MotorDynamicsLab/LDOVoron0/Images/Kirigami/a_side_cable_run.jpg

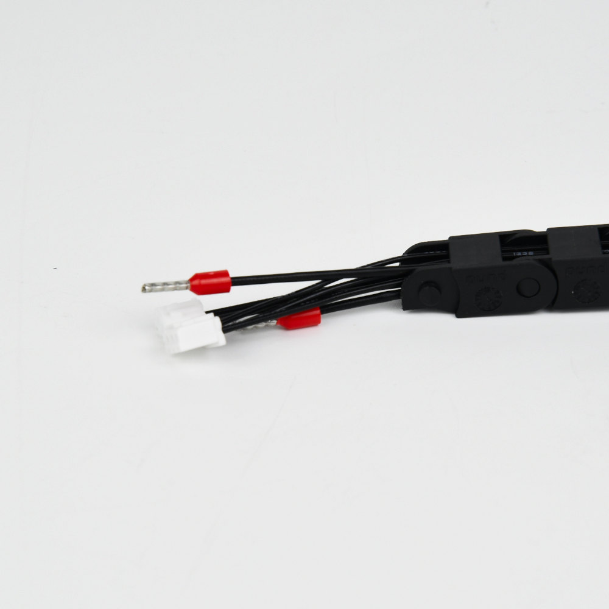
Images/Kirigami/a_side_cable_run.jpg
