MotorDynamicsLab/LDOVoron0/Images/Kirigami/cable_chain_skirt_anchor.JPG

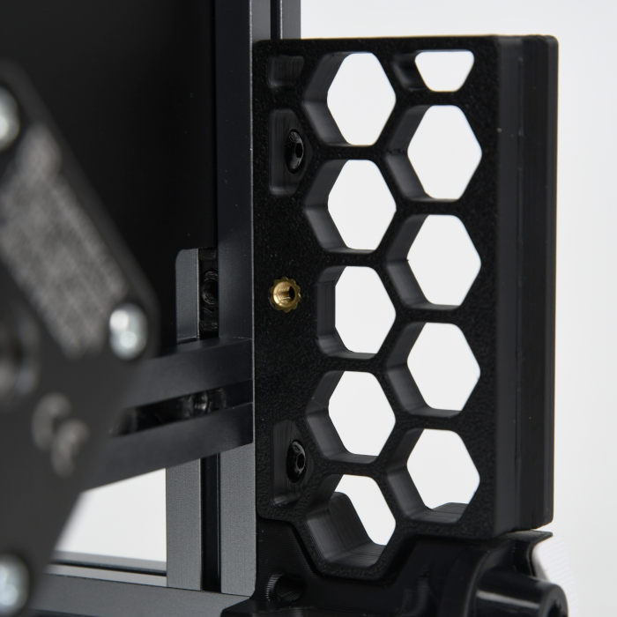
Images/Kirigami/cable_chain_skirt_anchor.JPG
