MotorDynamicsLab/LDOVoron0/Images/Kirigami/cable_ends_labelled.jpg

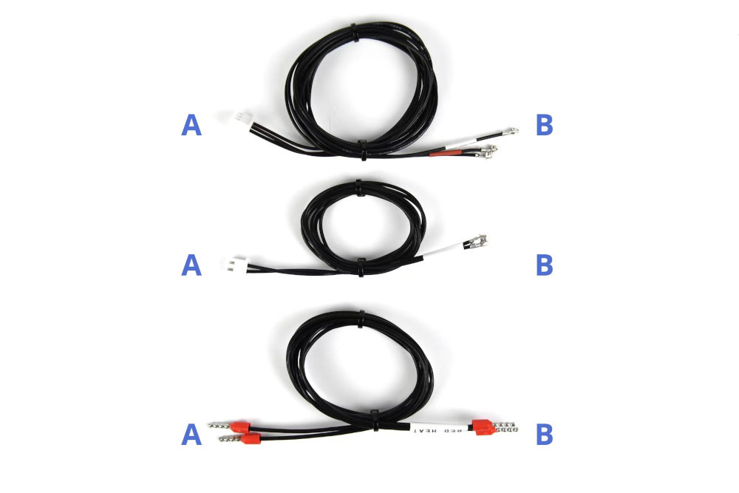
Images/Kirigami/cable_ends_labelled.jpg
