MotorDynamicsLab/LDOVoron0/Images/Kirigami/chain_end_locations.jpg

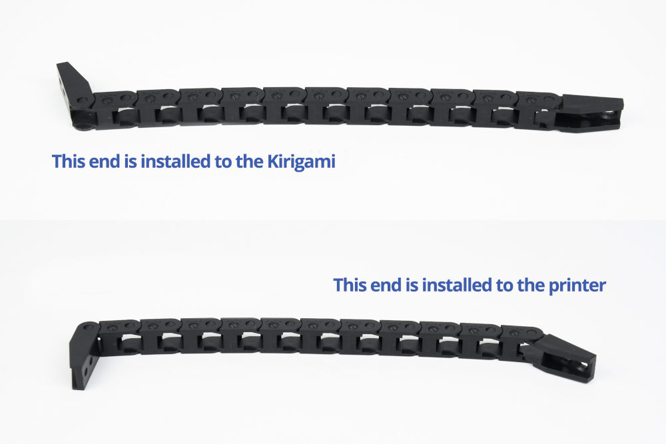
Images/Kirigami/chain_end_locations.jpg
