MotorDynamicsLab/LDOVoron0/Images/Kirigami/chain_ends_labelled.jpg

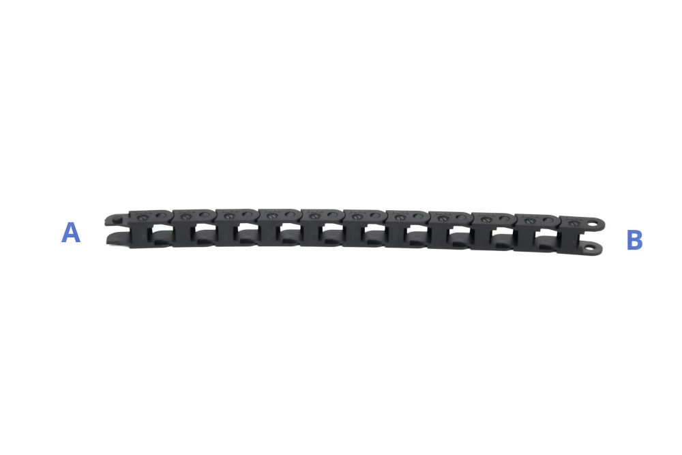
Images/Kirigami/chain_ends_labelled.jpg
