MotorDynamicsLab/LDOVoron0/Images/Kirigami/chain_height_check.JPG

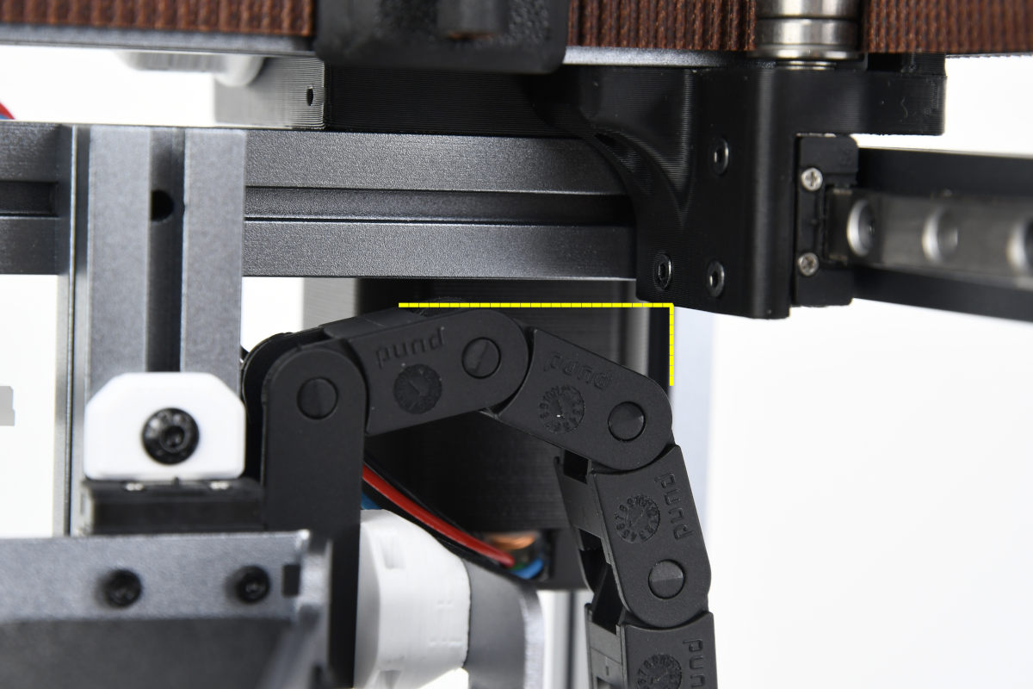
Images/Kirigami/chain_height_check.JPG
