MotorDynamicsLab/LDOVoron0/Images/Kirigami/neopixel_ziptied.JPG

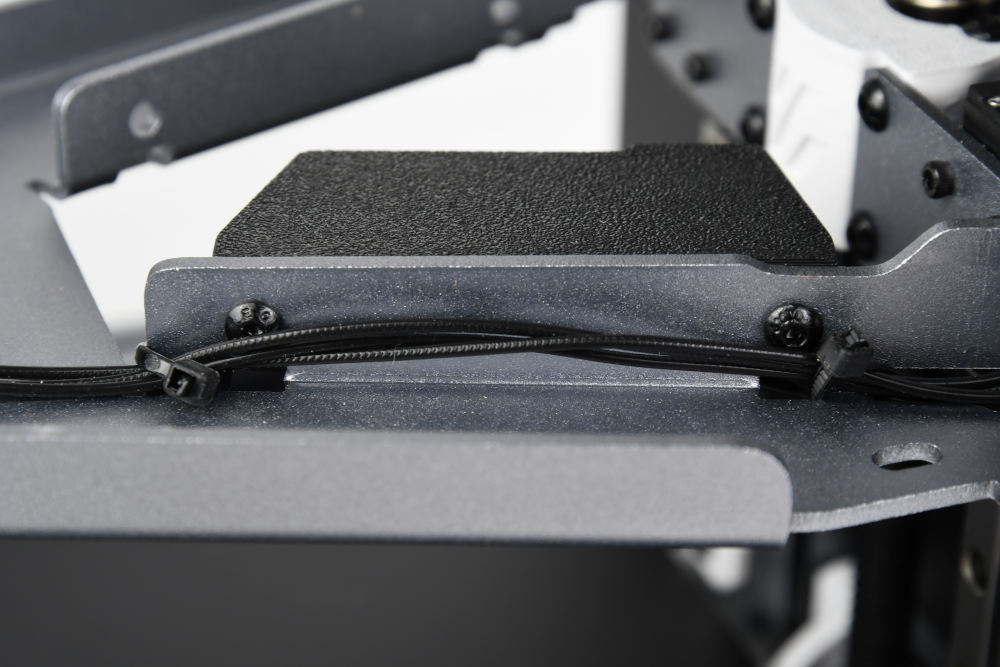
Images/Kirigami/neopixel_ziptied.JPG
