MotorDynamicsLab/LDOVoron0/Images/Kirigami/R1/bare_kirigami.jpg

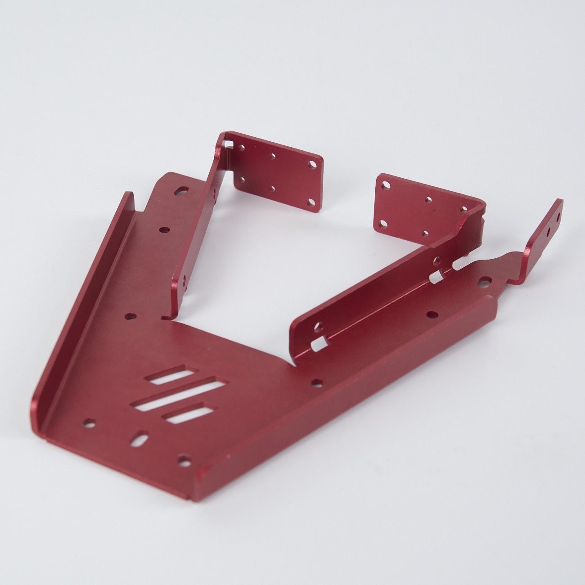
Images/Kirigami/R1/bare_kirigami.jpg
