MotorDynamicsLab/LDOVoron0/Images/Kirigami/R1/cable_layout_bottom.jpg

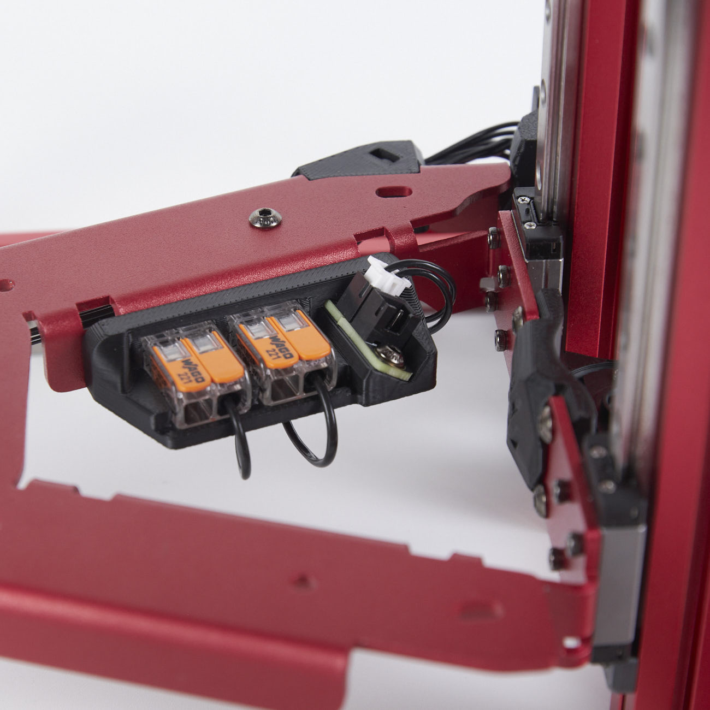
Images/Kirigami/R1/cable_layout_bottom.jpg
