MotorDynamicsLab/LDOVoron0/Images/Kirigami/R1/cable_layout_top.jpg

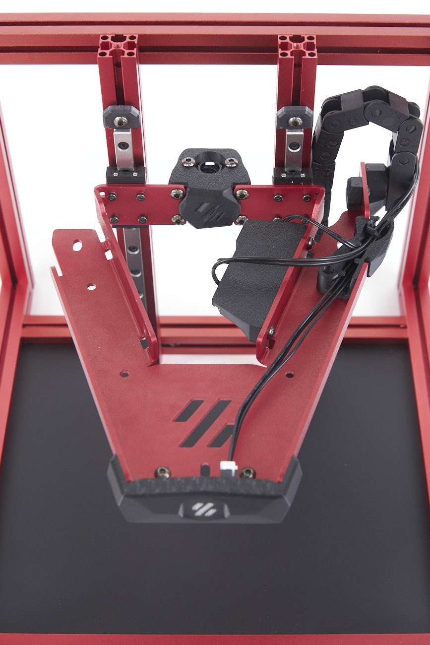
Images/Kirigami/R1/cable_layout_top.jpg
