MotorDynamicsLab/LDOVoron0/Images/Kirigami/R1/chain_mount.jpg

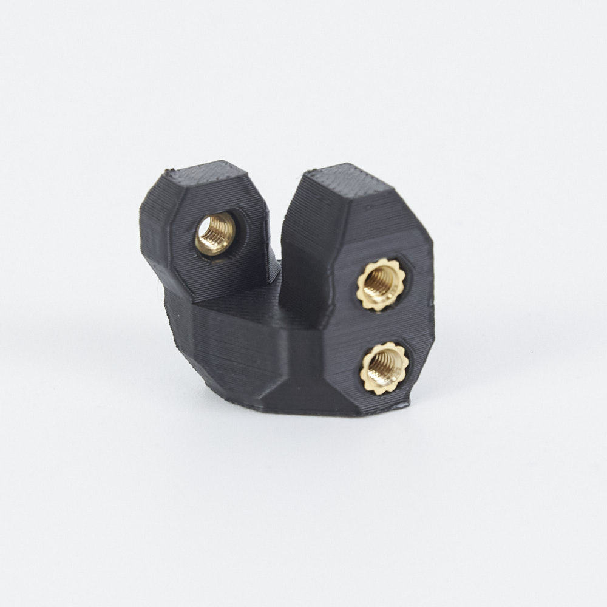
Images/Kirigami/R1/chain_mount.jpg
