MotorDynamicsLab/LDOVoron0/Images/Kirigami/R1/chain_with_cables.jpg

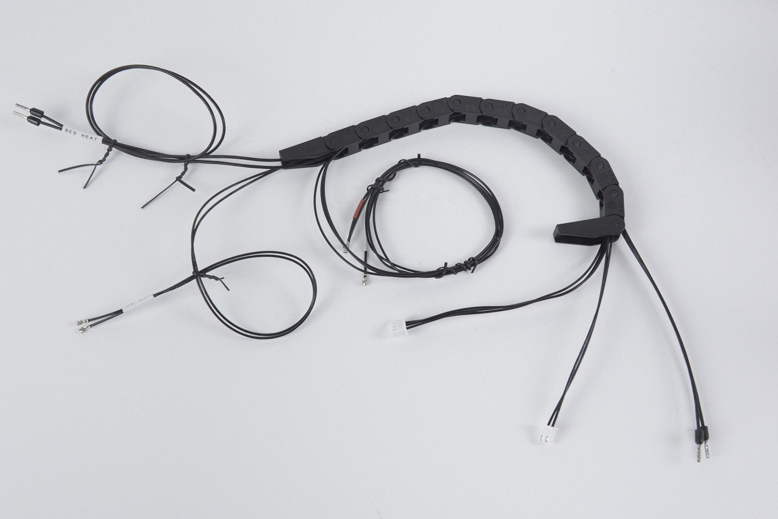
Images/Kirigami/R1/chain_with_cables.jpg
