MotorDynamicsLab/LDOVoron0/Images/Kirigami/R1/neopixel_pinout.jpg

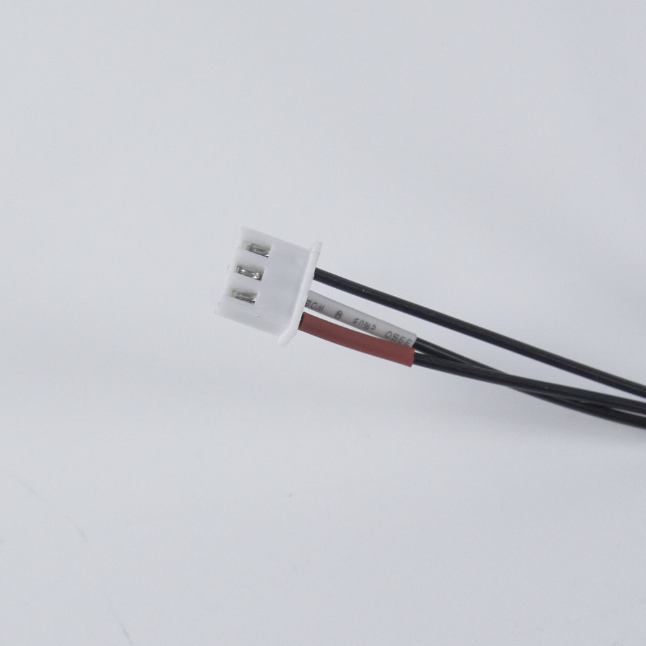
Images/Kirigami/R1/neopixel_pinout.jpg
