MotorDynamicsLab/LDOVoron0/Images/Kirigami/R1/nut_block_back.jpg

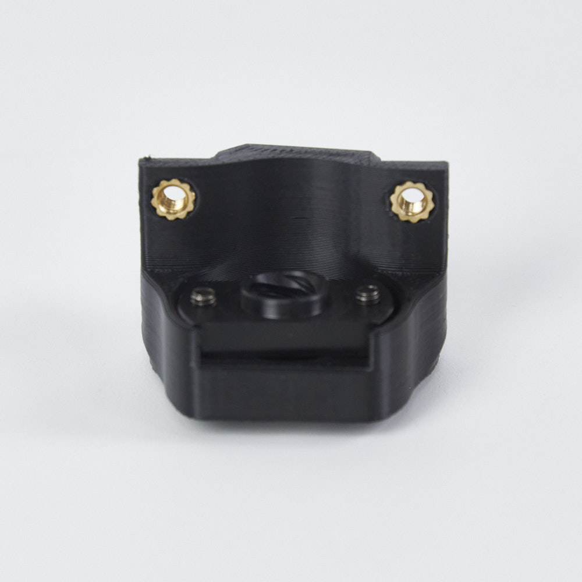
Images/Kirigami/R1/nut_block_back.jpg
