MotorDynamicsLab/LDOVoron0/Images/Kirigami/R1/nut_block_front.jpg

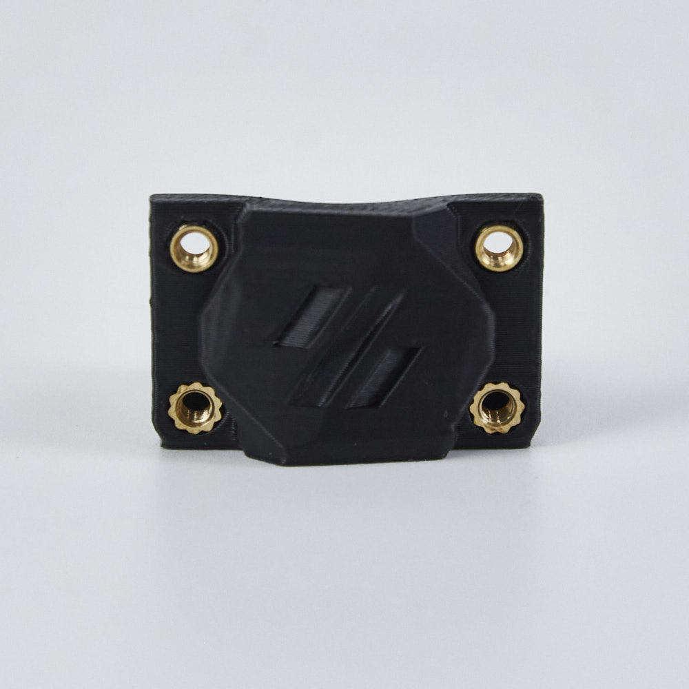
Images/Kirigami/R1/nut_block_front.jpg
