MotorDynamicsLab/LDOVoron0/Images/Kirigami/R1/sb_front_with_cable.jpg

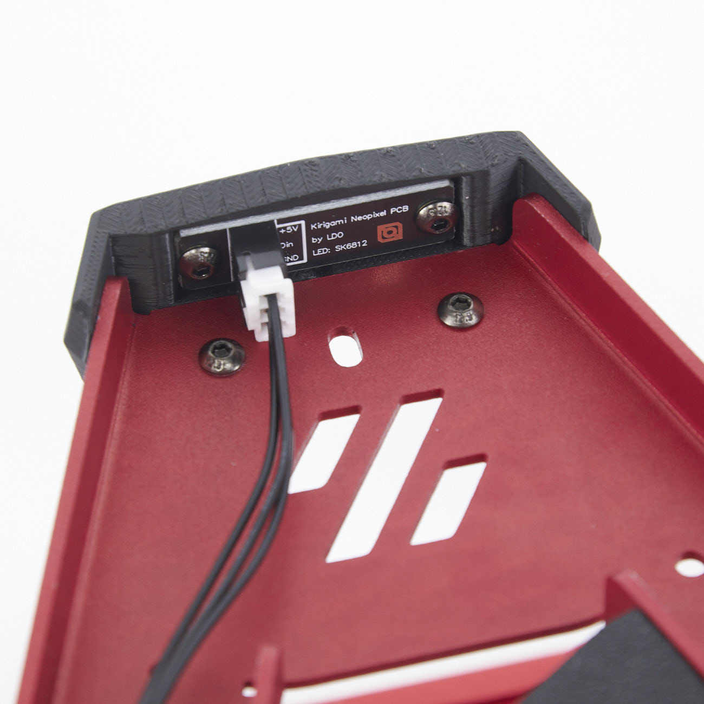
Images/Kirigami/R1/sb_front_with_cable.jpg
