MotorDynamicsLab/LDOVoron0/Images/Kirigami/R1/stealth_front_bottom.jpg

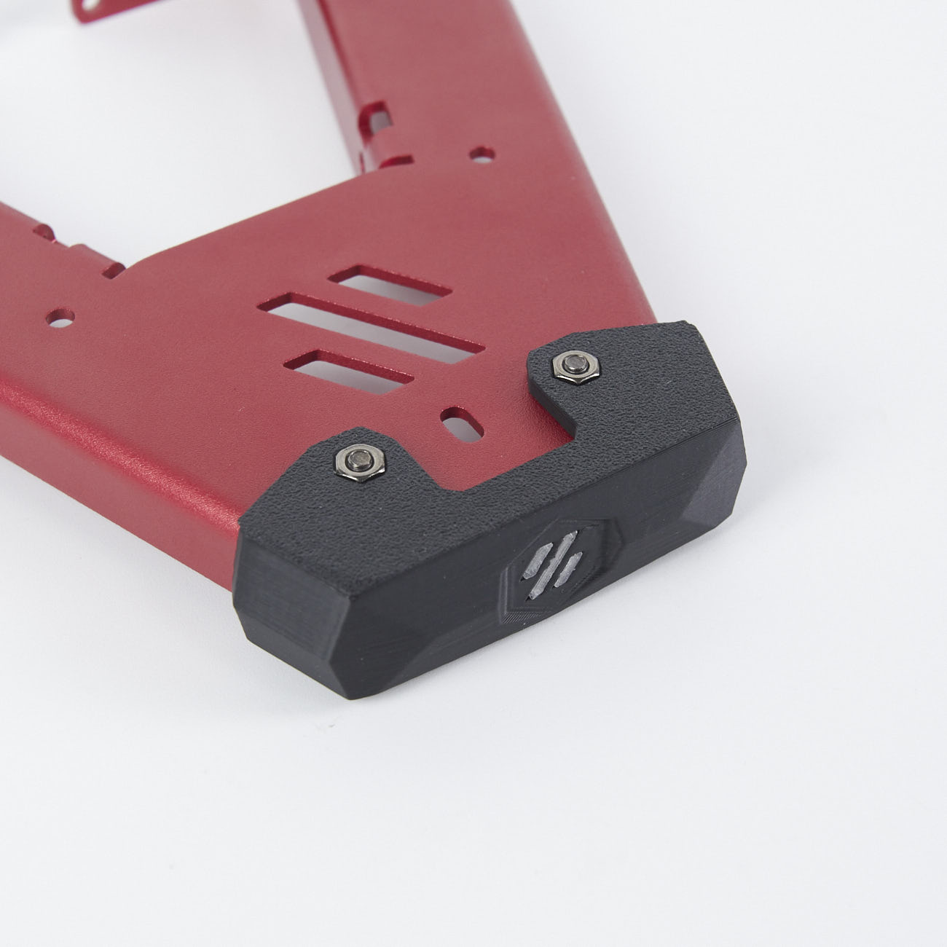
Images/Kirigami/R1/stealth_front_bottom.jpg
