MotorDynamicsLab/LDOVoron0/Images/Kirigami/R1/stealth_front_with_diffuser.jpg

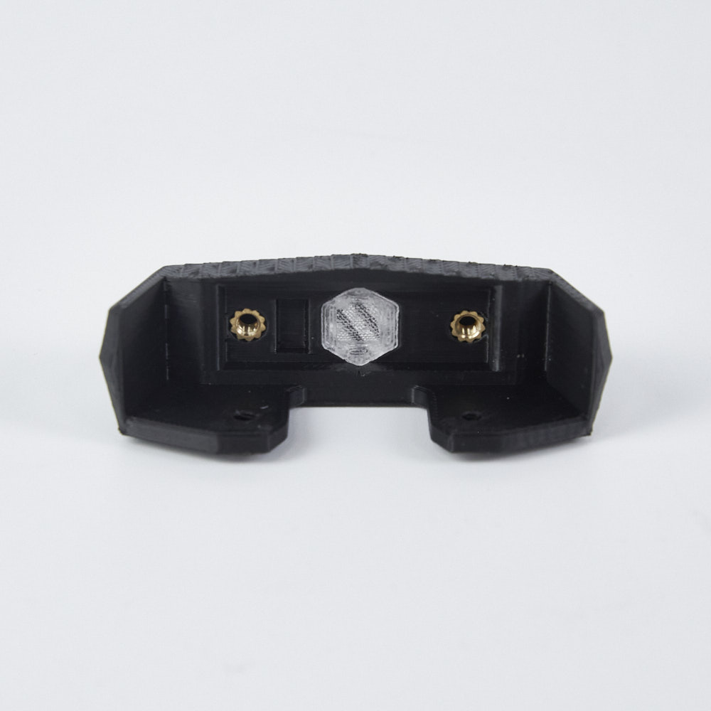
Images/Kirigami/R1/stealth_front_with_diffuser.jpg
