MotorDynamicsLab/LDOVoron0/Images/Kirigami/R1/stealth_front_with_pcb.jpg

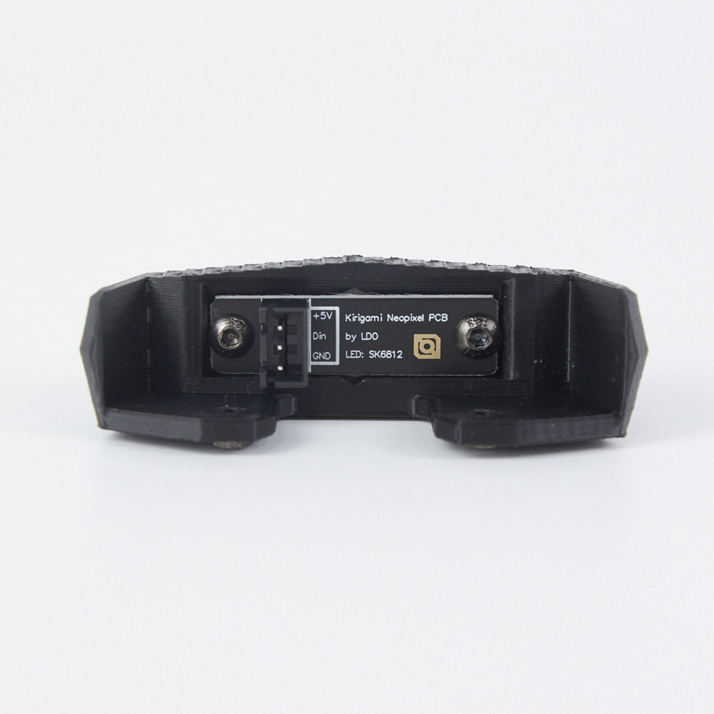
Images/Kirigami/R1/stealth_front_with_pcb.jpg
