MotorDynamicsLab/LDOVoron0/Images/Kirigami/R1/tramming_view.jpg

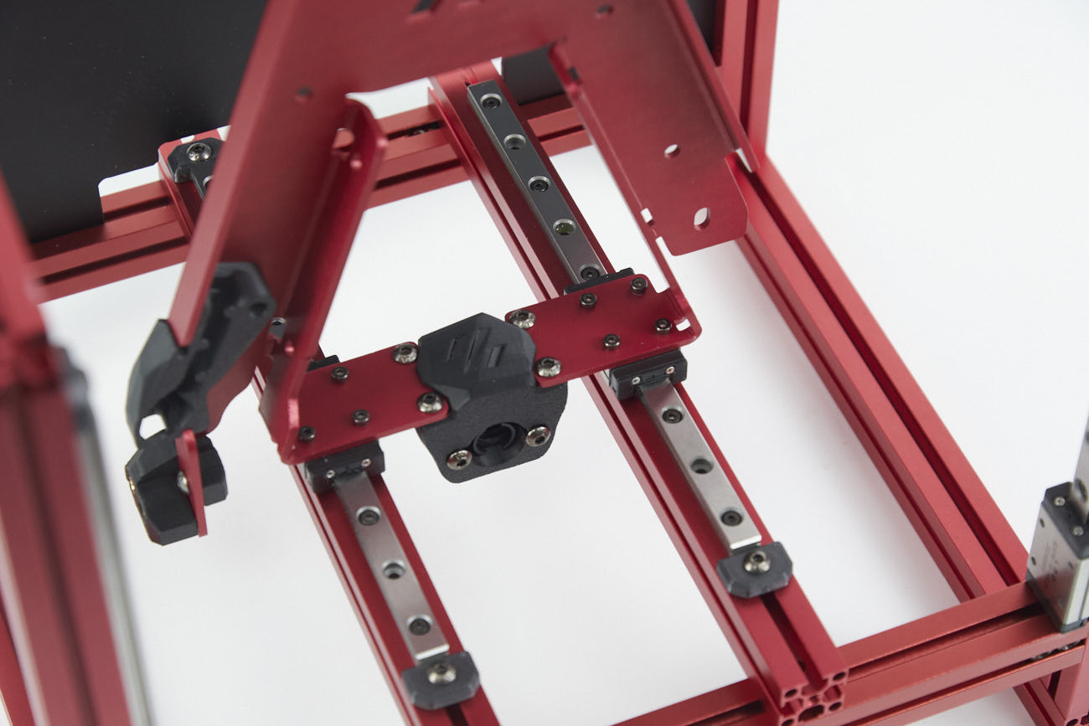
Images/Kirigami/R1/tramming_view.jpg
