MotorDynamicsLab/LDOVoron0/Images/Kirigami/R1/wago_mount_back.jpg

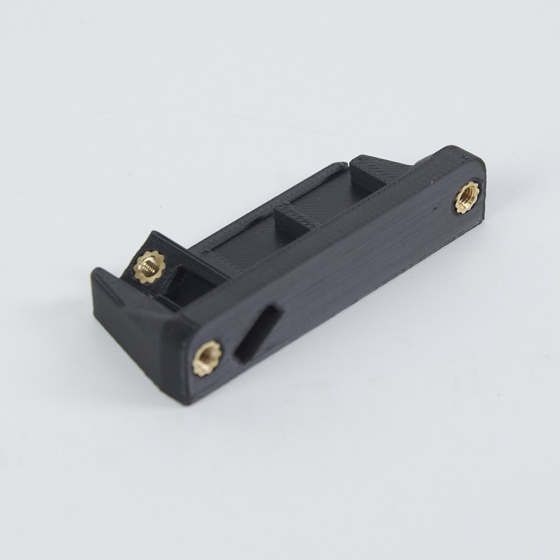
Images/Kirigami/R1/wago_mount_back.jpg
