MotorDynamicsLab/LDOVoron0/Images/Kirigami/R1/wago_mount_front.jpg

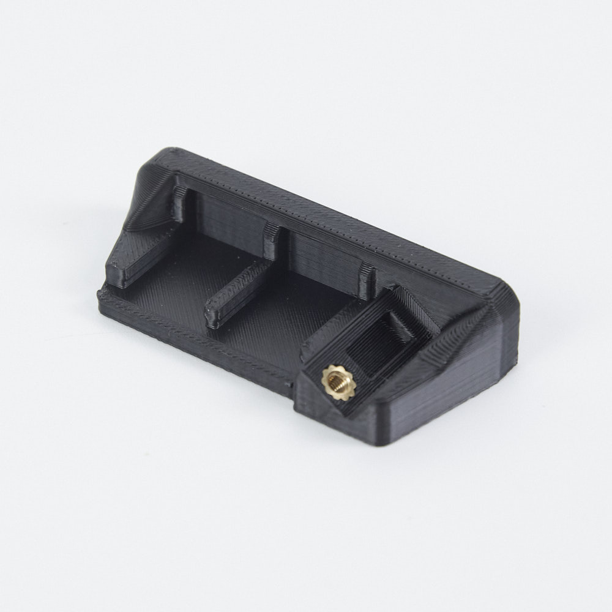
Images/Kirigami/R1/wago_mount_front.jpg
