MotorDynamicsLab/LDOVoron0/Images/split_rear_panel_cad.png

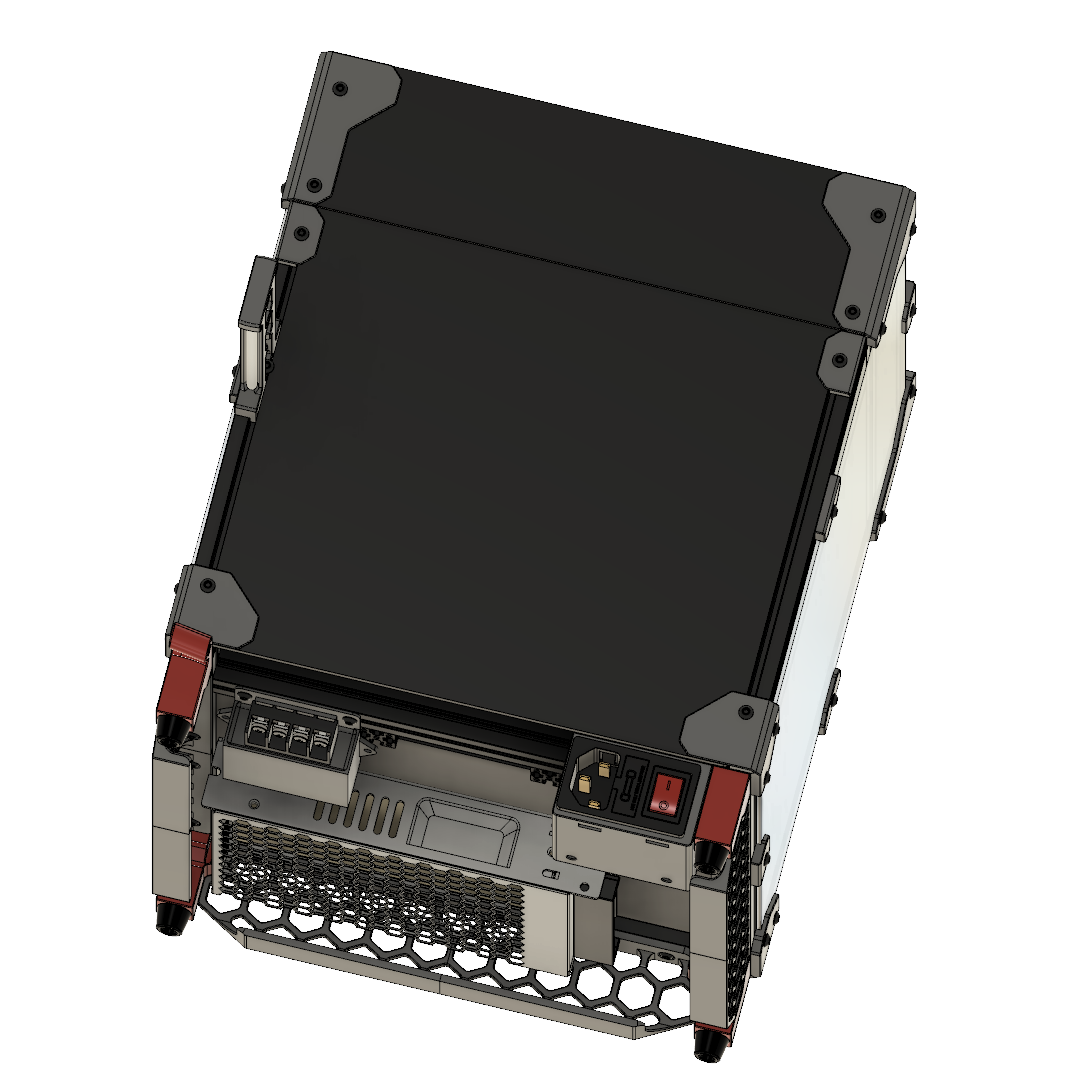
Images/split_rear_panel_cad.png
