MotorDynamicsLab/LDOVoron0/Images/Kirigami/R1/printed_parts_installed.jpg

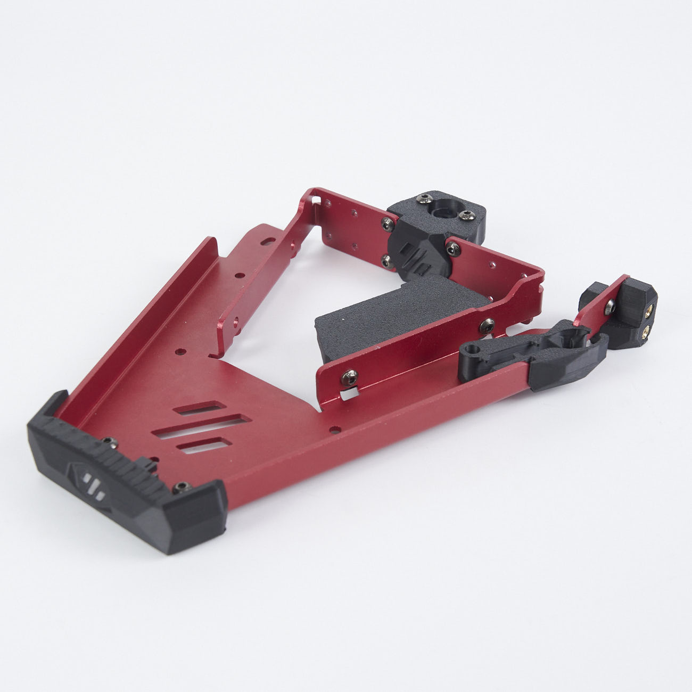
Images/Kirigami/R1/printed_parts_installed.jpg
