MotorDynamicsLab/LDOVoron0/STLs/Detachable_Spool_Holder/Spool_Holder.stl

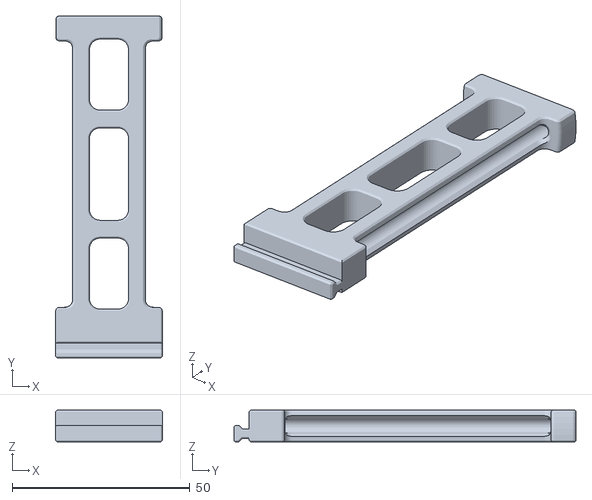
[picture p40: CAD file, 2023-02-16]
STLs/Detachable_Spool_Holder/Spool_Holder.stl
30.0 x 96.2 x 9.00
