MotorDynamicsLab/LDOVoron0/STLs/DIN_Mounts/SKR Pico Mount_x2.step

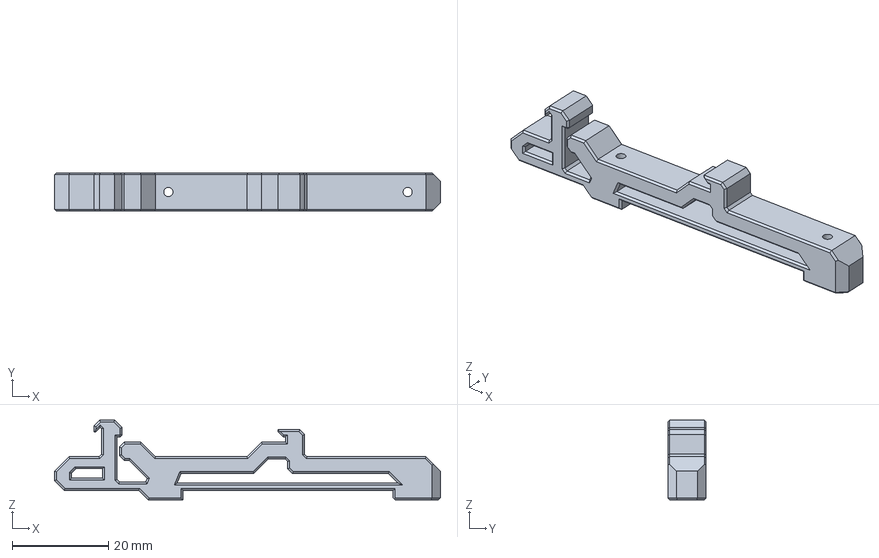
[picture p41: CAD file, 2023-02-05]
STLs/DIN_Mounts/SKR Pico Mount_x2.step
80.3 x 8.00 x 16.6 mm
