MotorDynamicsLab/LDOVoron0/STLs/Kirigami/Kirigami_LDO_Breakout_Mount.stl

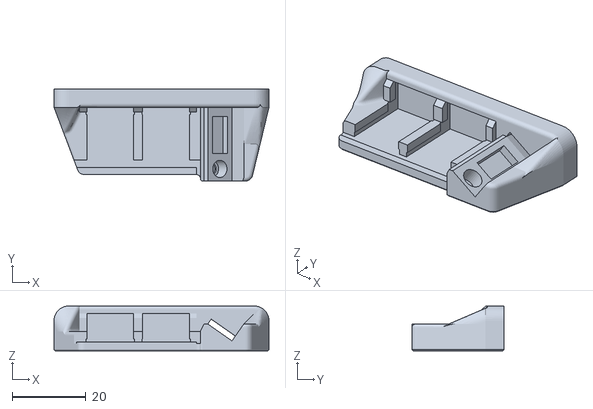
[picture p42: CAD file, 2023-02-16]
STLs/Kirigami/Kirigami_LDO_Breakout_Mount.stl
58.3 x 25.0 x 12.2
