MotorDynamicsLab/LDOVoron0/STLs/Name_Plate/Name_Plate_Top.stl

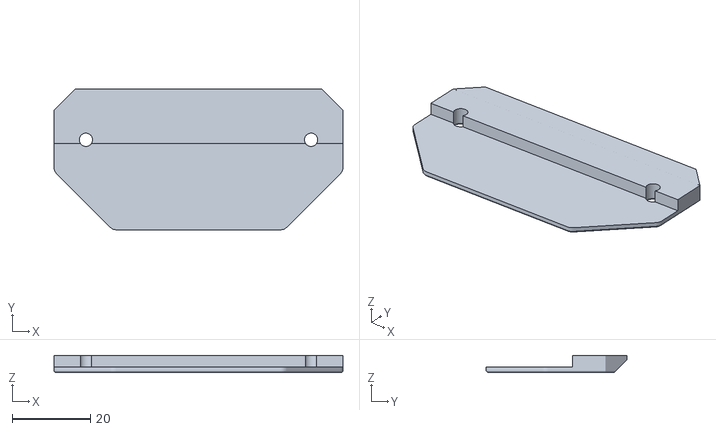
[picture p43: CAD file, 2023-02-16]
STLs/Name_Plate/Name_Plate_Top.stl
73.8 x 35.9 x 4.42
