MotorDynamicsLab/LDOVoron0/STLs/Picobilical_Toolhead/Picobilical_Strain_Relief_Spacer_A.stl

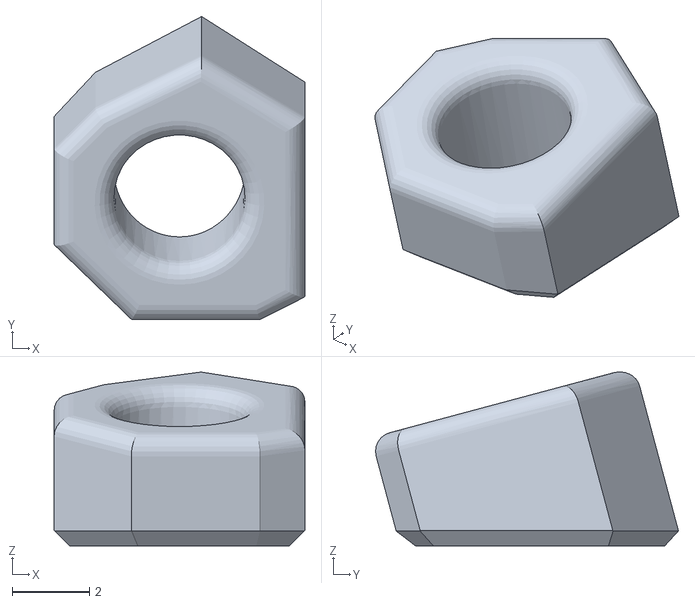
[picture p44: CAD file, 2023-02-16]
STLs/Picobilical_Toolhead/Picobilical_Strain_Relief_Spacer_A.stl
6.50 x 7.85 x 4.51
