MotorDynamicsLab/LDOVoron0/STLs/Preset_Print_PlatesR1/LDO_Electronics_Tools_Inlet_PlateR1.3mf

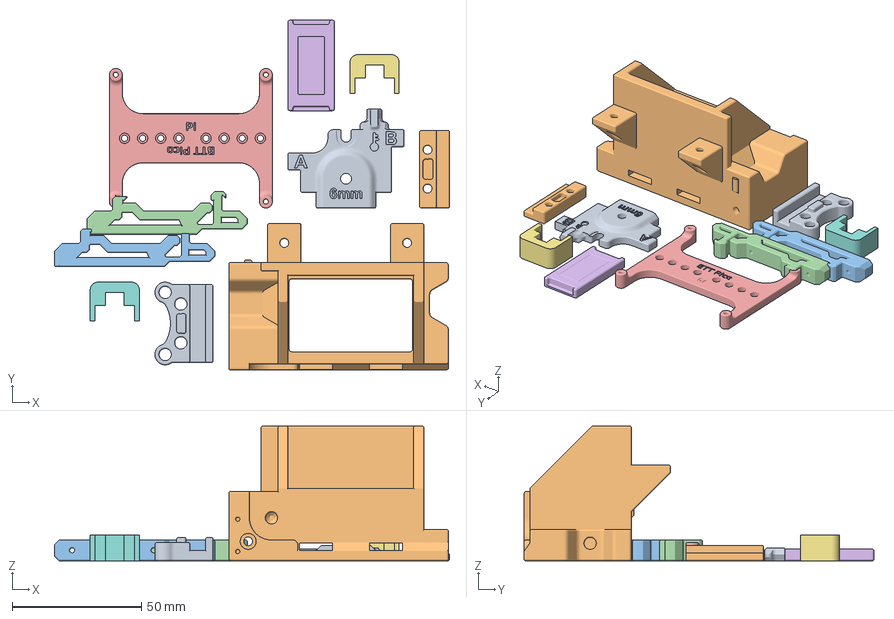
[picture p45: CAD file, 2023-06-14]
STLs/Preset_Print_PlatesR1/LDO_Electronics_Tools_Inlet_PlateR1.3mf
152.6 x 135.1 x 52.0 mm
Fan_Mount_Bottom_x1.stl
Fan_Mount_Top_x1.stl
PCB_DIN_Clip_x2.stl
RPi_or_BTT-Pico_Mount.STL
VHB_DIN_Mount.STL
MGN7_Rail_Guide_x2.STL
Swiss_Army_Jig_x1.STL
V02R1_Mains_Inlet Foot_1_2mm.stl
