MotorDynamicsLab/LDOVoron0/STLs/Picobilical_Toolhead/Picobilical_Strain_Relief_Extender_x2.stl

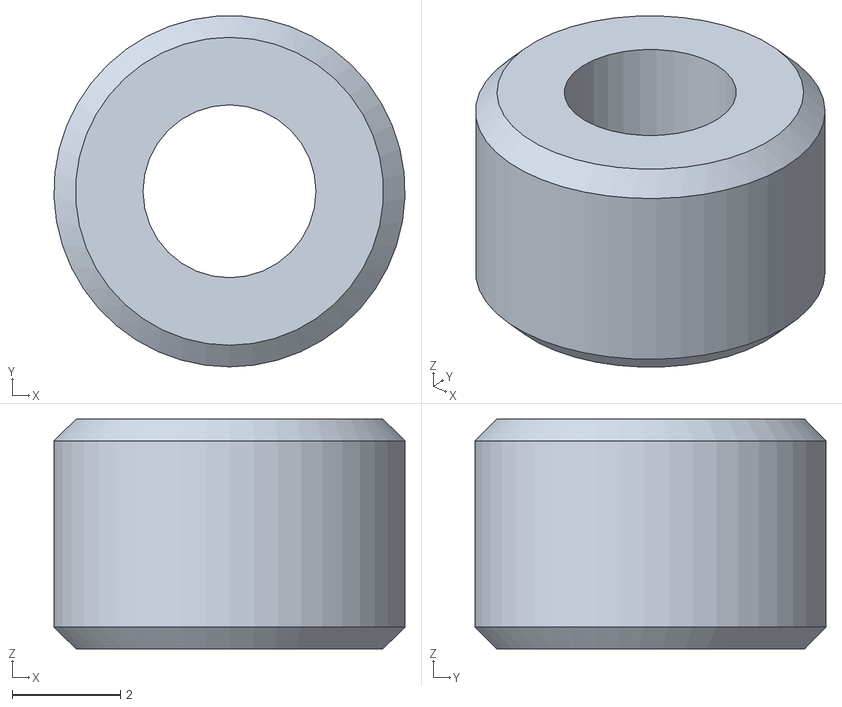
[picture p47: CAD file, 2023-02-16]
STLs/Picobilical_Toolhead/Picobilical_Strain_Relief_Extender_x2.stl
6.50 x 6.49 x 4.25
