MotorDynamicsLab/LDOVoron0/STLs/Preset_Print_PlatesR1/LDO_Skirts_PlateR1.3mf

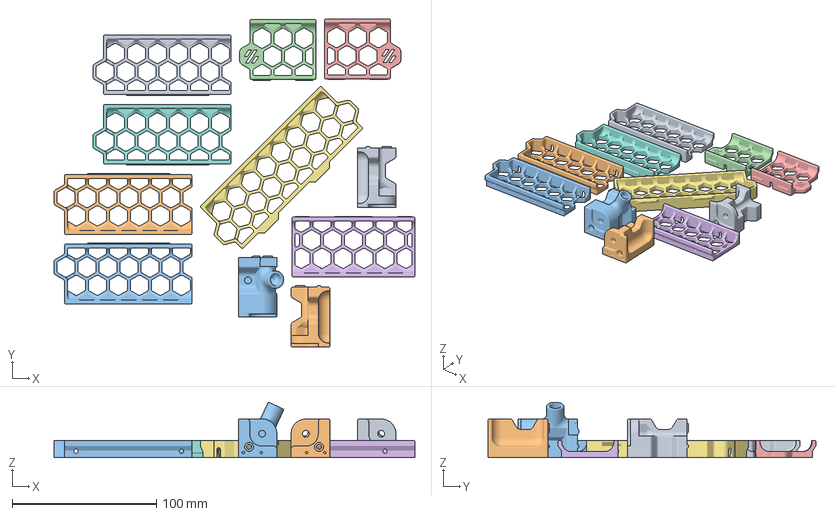
[picture p48: CAD file, 2023-06-14]
STLs/Preset_Print_PlatesR1/LDO_Skirts_PlateR1.3mf
250.0 x 227.2 x 38.4 mm
Foot_Front_Left_x1.STL
Foot_Front_Right_x1.STL
Foot_Rear_Right_FRS_x1.STL
Front_Skirt_A_x1.STL
Front_Skirt_B_x1.STL
Headless_Skirt_Insert.STL
Rear_Skirt_x1.STL
Side_Skirt_Mirror_x2.stl
Side_Skirt_x2.STL
