MotorDynamicsLab/LDOVoron0/STLs/Name_Plate/Name_Plate.stl

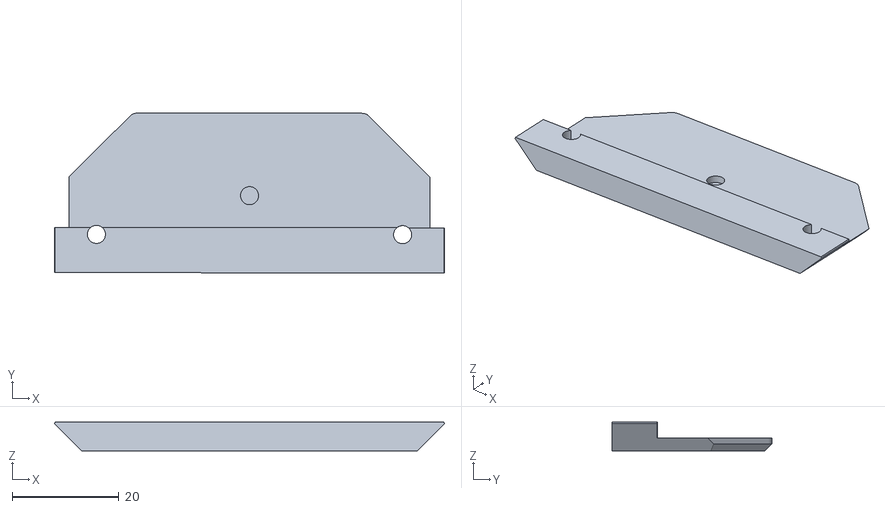
[picture p49: CAD file, 2023-02-16]
STLs/Name_Plate/Name_Plate.stl
73.2 x 30.0 x 5.40
