MotorDynamicsLab/LDOVoron0/STLs/Picobilical_Toolhead/Picobilical_Strain_Relief_Spacer_B.stl

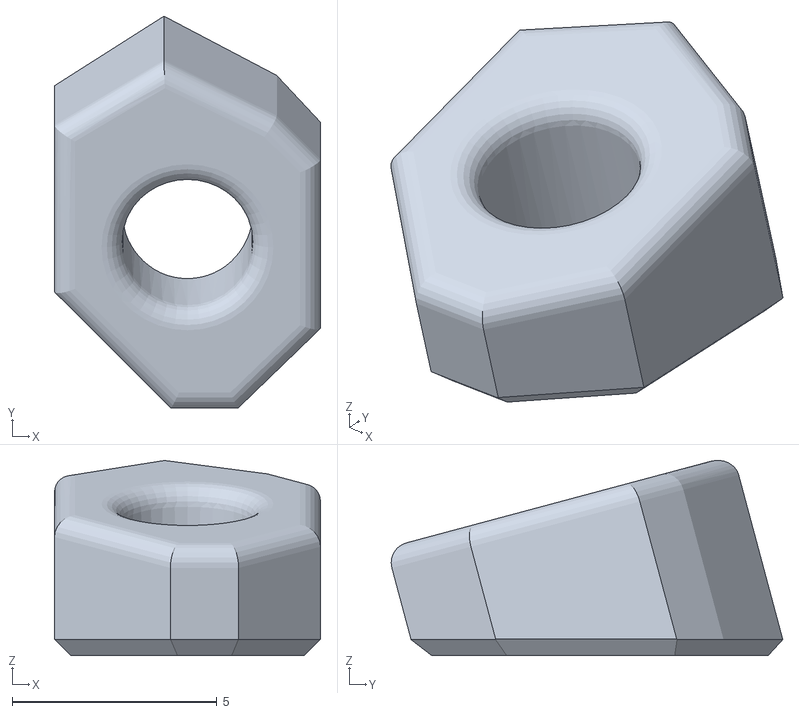
[picture p50: CAD file, 2023-02-16]
STLs/Picobilical_Toolhead/Picobilical_Strain_Relief_Spacer_B.stl
6.50 x 9.57 x 4.77
