MotorDynamicsLab/LDOVoron0/STLs/Picobilical_Toolhead/Picobilical Toolhead Mount V02.step

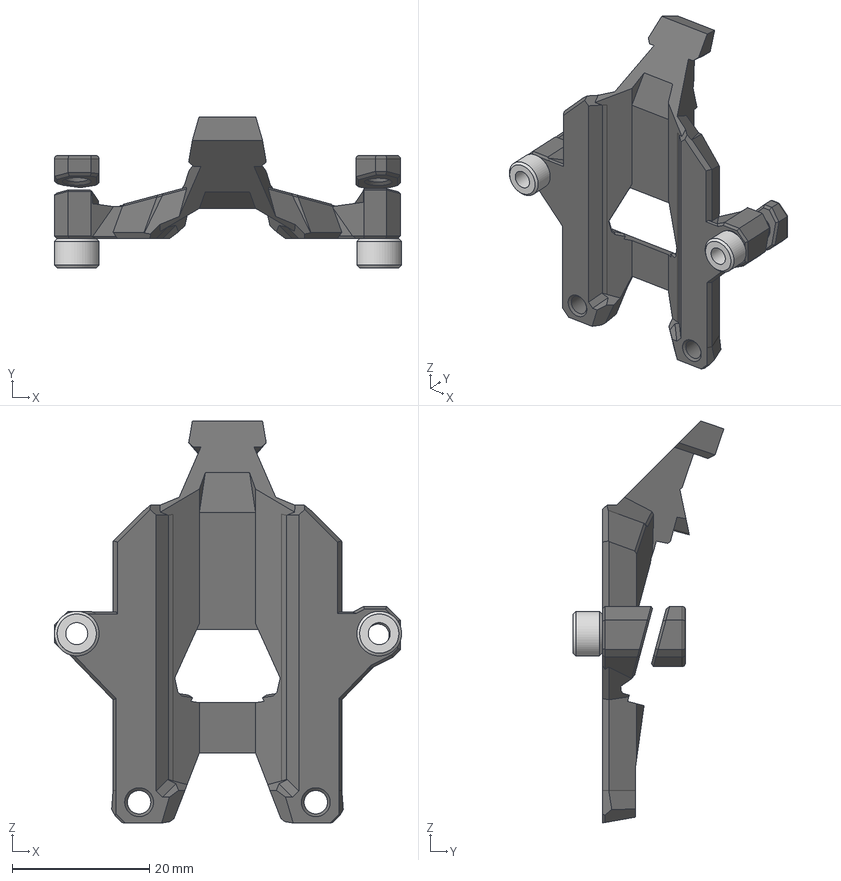
[picture p51: CAD file, 2023-02-05]
STLs/Picobilical_Toolhead/Picobilical Toolhead Mount V02.step
50.5 x 21.9 x 58.5 mm
