MotorDynamicsLab/LDOVoron0/STLs/Preset_Print_PlatesR1/LDO_Custom_PlateR1.3mf

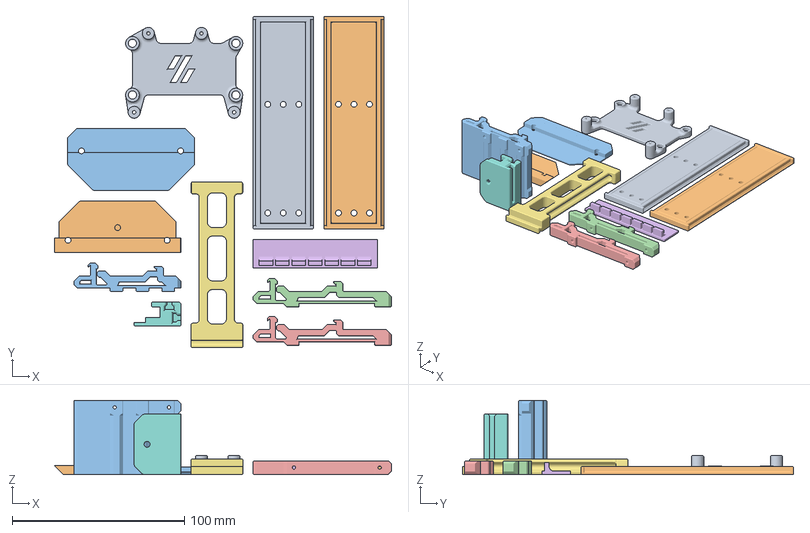
[picture p52: CAD file, 2023-06-14]
STLs/Preset_Print_PlatesR1/LDO_Custom_PlateR1.3mf
195.5 x 192.3 x 43.0 mm
DIN Screw Cleat_x2
DIN Screw Cleat_x2.stl
Pi Expansion Clips.stl
SKR Pico Mount_x2.stl
Mornsun_PSU_Cover
Spool_Holder.stl
Spool_Holder_Mount.stl
RPi_Zero_USB_Expander_Mount.stl
Name_Plate.stl
Name_Plate_Top_Logo.stl
