MotorDynamicsLab/LDOVoron0/STLs/Preset_Print_PlatesR1/LDO_Panel_Mounting_PlateR1.3mf

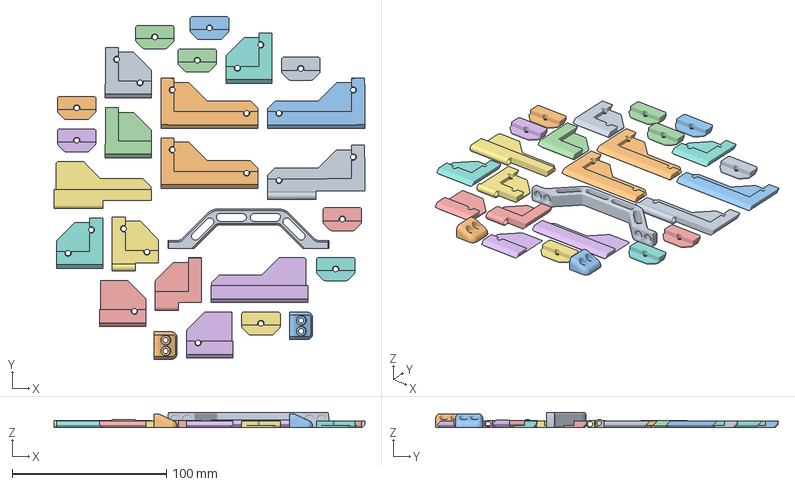
[picture p53: CAD file, 2023-06-14]
STLs/Preset_Print_PlatesR1/LDO_Panel_Mounting_PlateR1.3mf
201.0 x 222.0 x 10.0 mm
Door_Handle_x1.STL
Door_Latch_x2.STL
Front_Bottom_Left_Clip_x1.stl
Front_Bottom_Right_Hinge_x1.stl
Front_Top_Left_Clip_x1.stl
Front_Top_Right_Hinge_x1.stl
Left_Bottom_Front_Panel_Clip_x1.stl
Left_Bottom_Rear_Panel_Clip_x1.stl
Left_Top_Front_Panel_Clip_x1.stl
Left_Top_Rear_Panel_Clip_x1.stl
Middle_Clip_x9.stl
Rear_Bottom_Left_Clip_x1.stl
Rear_Bottom_Right_Clip_x1.stl
Right_Bottom_Front_Hinge_x1.stl
Right_Bottom_Rear_Panel_Clip_x1.stl
Right_Top_Left_Hinge_x1.stl
Right_Top_Rear_Panel_Clip_x1.stl
