MotorDynamicsLab/LDOVoron0/STLs/Preset_Print_PlatesR1/LDO_Picobilical_PlateR1.3mf

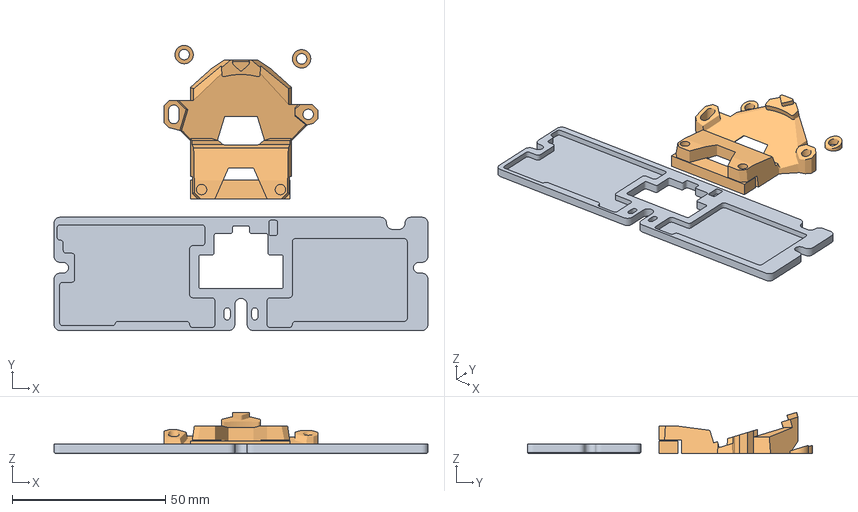
[picture p54: CAD file, 2023-06-14]
STLs/Preset_Print_PlatesR1/LDO_Picobilical_PlateR1.3mf
122.0 x 93.0 x 13.5 mm
frame_cover_plate.stl
toolhead_spacer_v02.stl
