MotorDynamicsLab/LDOVoron0/STLs/Preset_Print_PlatesR1/LDO_NoDropNut_PlateR1.3mf

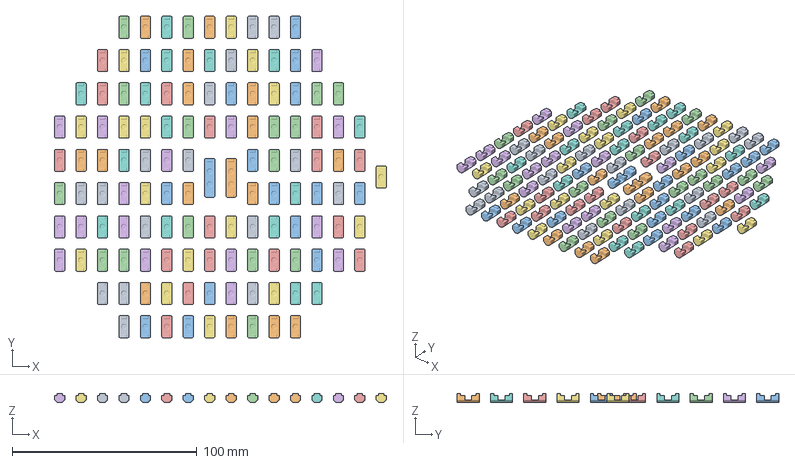
[picture p55: CAD file, 2023-06-14]
STLs/Preset_Print_PlatesR1/LDO_NoDropNut_PlateR1.3mf
179.6 x 174.0 x 5.00 mm
NoDropNut_12mm.stl x 5
NoDropNut_Door_Latch_x2.stl
