MotorDynamicsLab/LDOVoron0/STLs/Preset_Print_PlatesR1/LDO_Mods_KirigamiR1.3mf

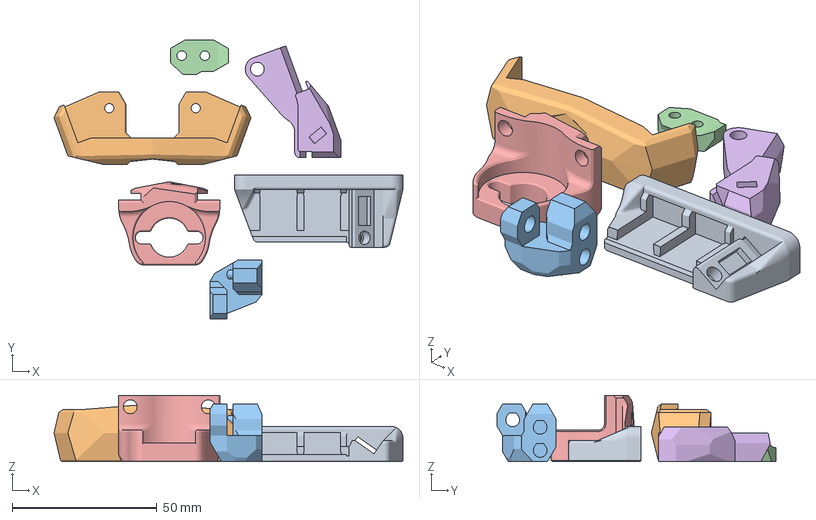
[picture p56: CAD file, 2023-06-14]
STLs/Preset_Print_PlatesR1/LDO_Mods_KirigamiR1.3mf
120.8 x 96.7 x 23.0 mm
Kirigami_LDO_Breakout_Mount.stl
Stealth_Bed_Main_Body.stl
VORON_v0.2_stealth_chain_mount.stl
VORON_v0.2_stealth_chain_mount_5mm_spacer.stl
VORON_v0.2_stealth_nut_block.stl
VORON_v0.2_stealth_wire_guide.stl
