MotorDynamicsLab/LDOVoron0/STLs/Preset_Print_PlatesR1/LDO_[a]_Toolheads_Skirts_Electronics_PlateR1.3mf

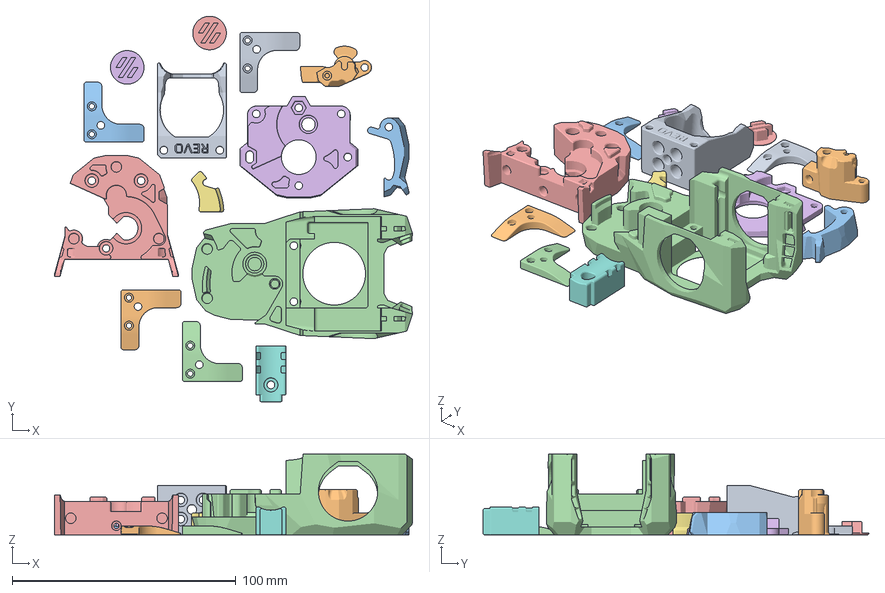
[picture p57: CAD file, 2023-06-14]
STLs/Preset_Print_PlatesR1/LDO_[a]_Toolheads_Skirts_Electronics_PlateR1.3mf
160.0 x 172.3 x 36.1 mm
[a]_FS_Hotend_Mount_Revo_Voron.stl
[a]_Guidler_x1.STL
[a]_Latch_x1.stl
[a]_MiniSB_Cowling_x1.STL
[a]_MiniSB_MidBody_x1.STL
[a]_MiniSB_Motor_Plate_x1.stl
[a]_Shuttle_x1.stl
[a]_Cable_Tie_x1.stl
[a]_Foot_Accent_A_x2.stl
[a]_Foot_Accent_B_x2.stl
[a]_Logo_Insert_x2.stl
