MotorDynamicsLab/LDOVoron0/STLs/Preset_Print_PlatesR1/LDO_Tophat_PlateR1.3mf

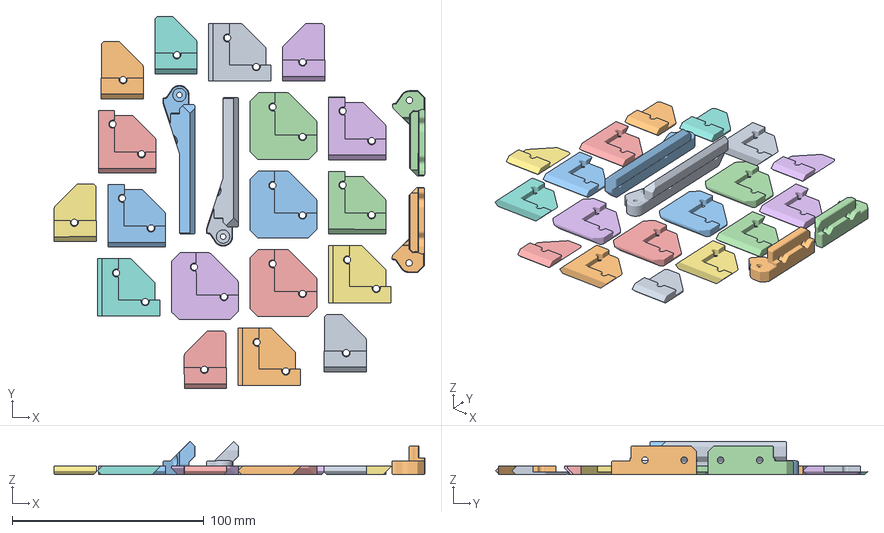
[picture p58: CAD file, 2023-06-14]
STLs/Preset_Print_PlatesR1/LDO_Tophat_PlateR1.3mf
193.3 x 194.0 x 17.2 mm
TH_Hinge_A_Bottom_x1.stl
TH_Hinge_A_Top_x1.stl
TH_Hinge_B_Bottom_x1.stl
TH_Hinge_B_Top_x1.stl
TH_Lower_Clip_Mirror_x3.stl
TH_Lower_Clip_x3.stl
TH_Side_Clip_Mirror_x4.stl
TH_Side_Clip_x4.stl
TH_Top_Clip_x4.stl
