MotorDynamicsLab/LDOVoron0/Images/Kirigami/chain_cables_installed_to_wago.JPG

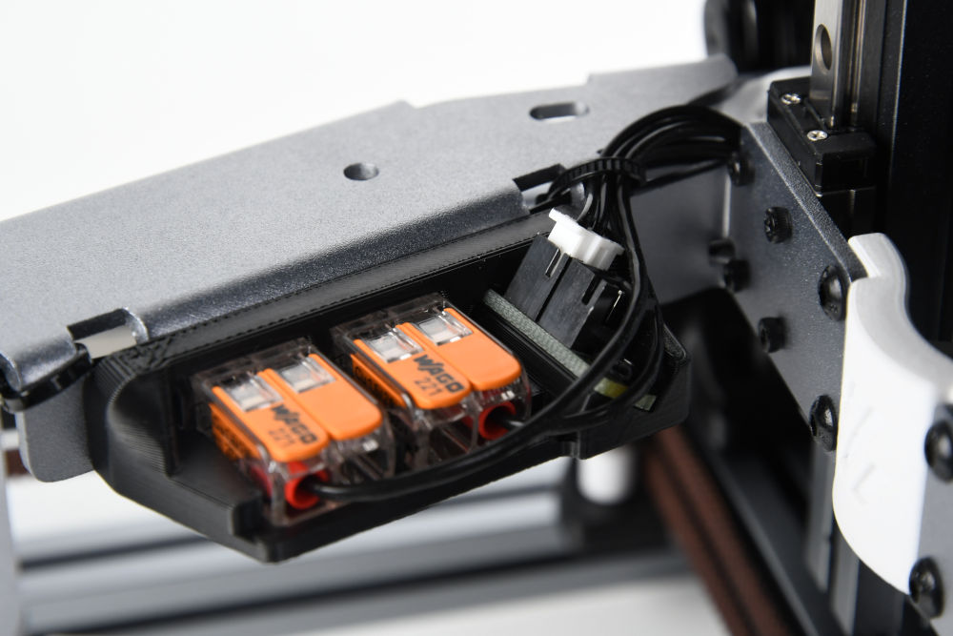
Images/Kirigami/chain_cables_installed_to_wago.JPG
