MotorDynamicsLab/LDOVoron0/Images/Kirigami/chain_end_installed_on_kirigami.jpg

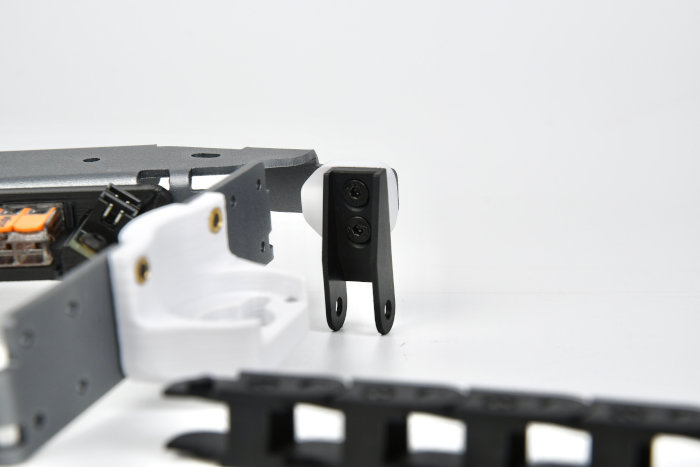
Images/Kirigami/chain_end_installed_on_kirigami.jpg
