MotorDynamicsLab/LDOVoron0/Images/Kirigami/final_wiring.JPG

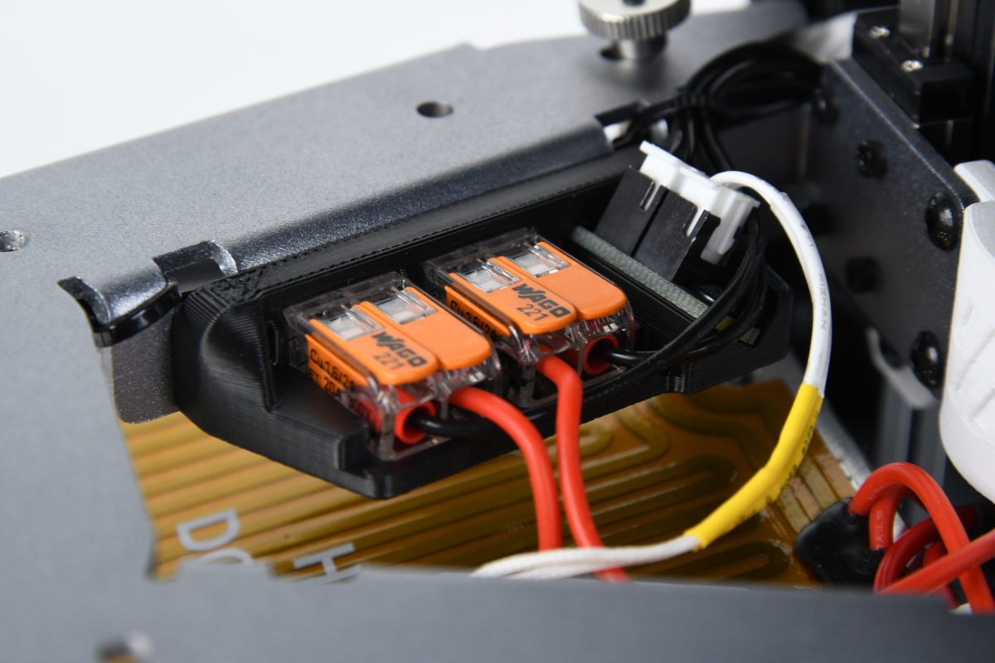
Images/Kirigami/final_wiring.JPG
