MotorDynamicsLab/LDOVoron0/Images/Kirigami/neopixel_housing_installed.JPG

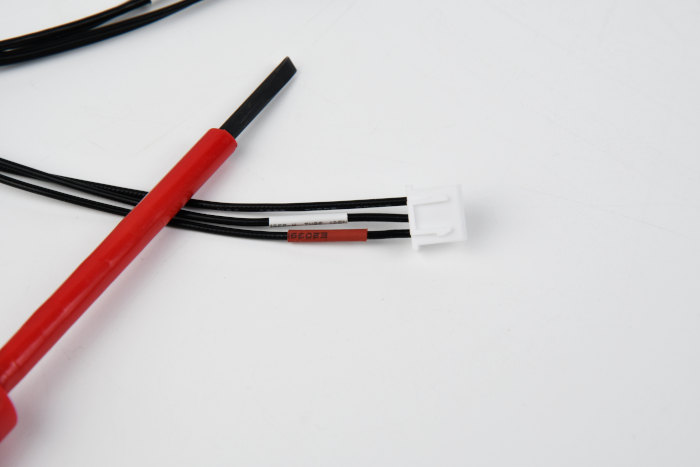
Images/Kirigami/neopixel_housing_installed.JPG
