MotorDynamicsLab/LDOVoron0/Images/Kirigami/R1/kirigami_installed_front.jpg

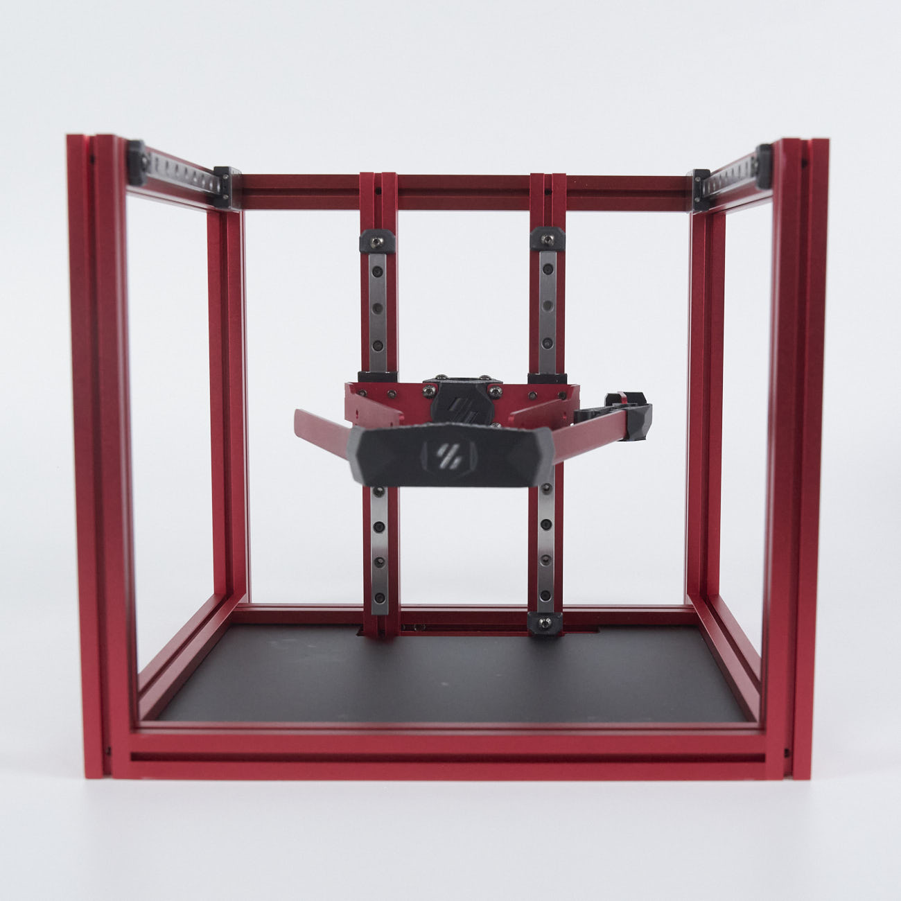
Images/Kirigami/R1/kirigami_installed_front.jpg
