MotorDynamicsLab/LDOVoron0/Images/Kirigami/R1/stealth_front_install.jpg

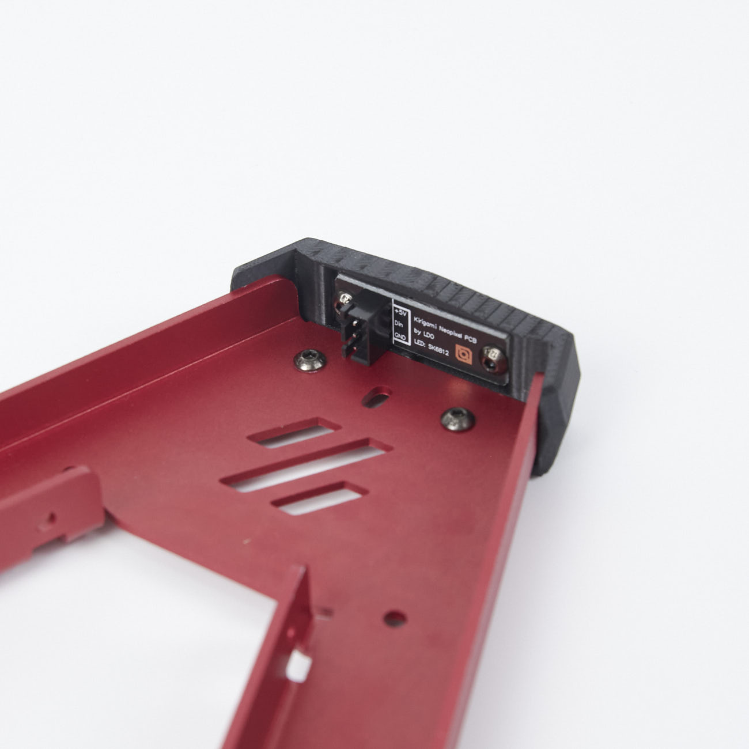
Images/Kirigami/R1/stealth_front_install.jpg
