MotorDynamicsLab/LDOVoron0/Images/Kirigami/R1/wago_mount_installed.jpg

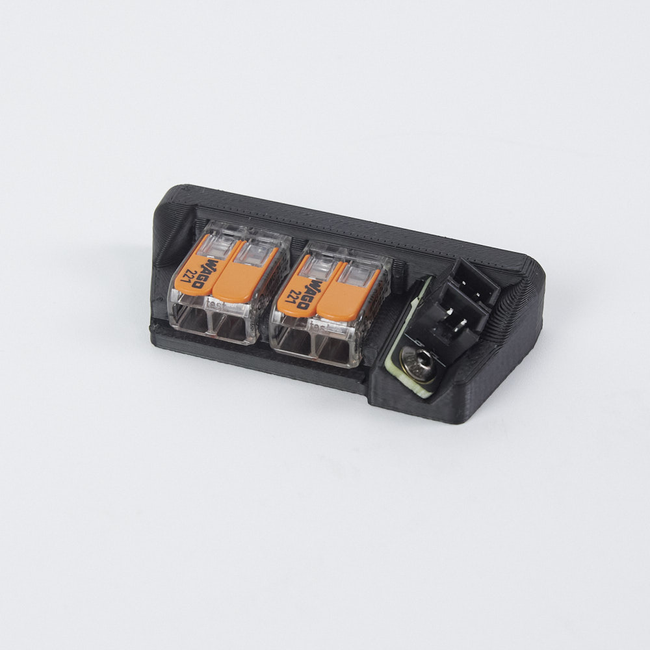
Images/Kirigami/R1/wago_mount_installed.jpg
