MotorDynamicsLab/LDOVoron0/Images/Kirigami/R1/wire_guide.jpg

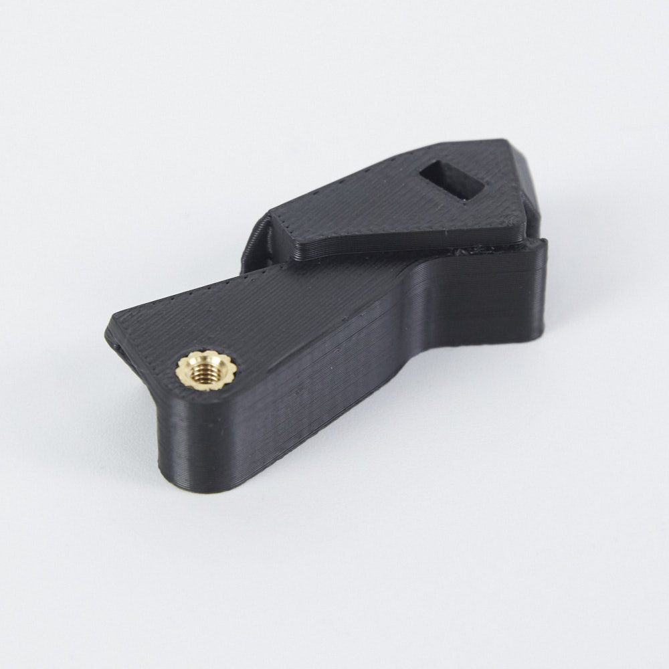
Images/Kirigami/R1/wire_guide.jpg
