MotorDynamicsLab/LDOVoron0/Images/WiringGuide/elec1_complete.jpg

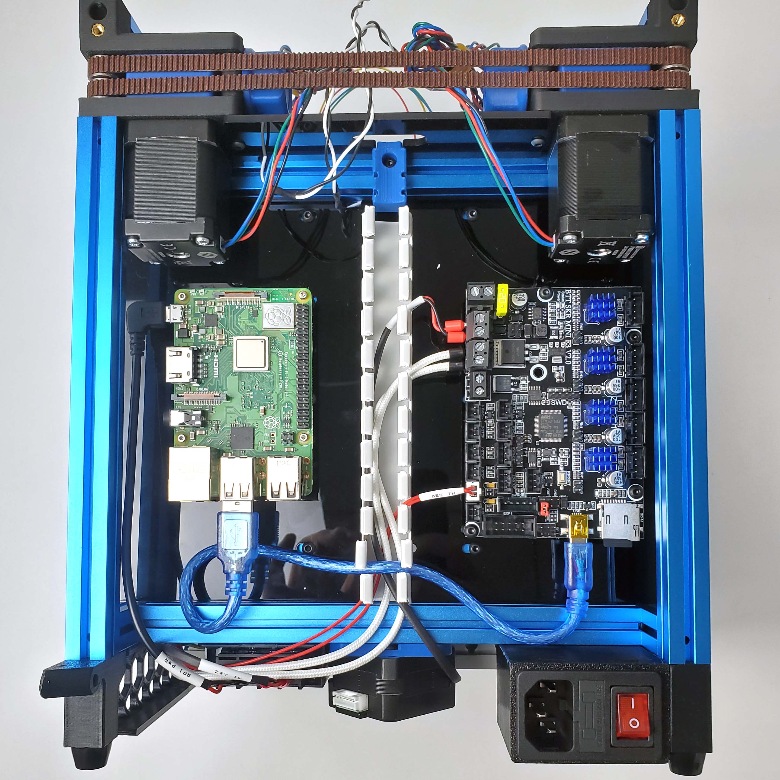
Images/WiringGuide/elec1_complete.jpg
