MotorDynamicsLab/LDOVoron0/Images/WiringGuide/elec2_complete.jpg

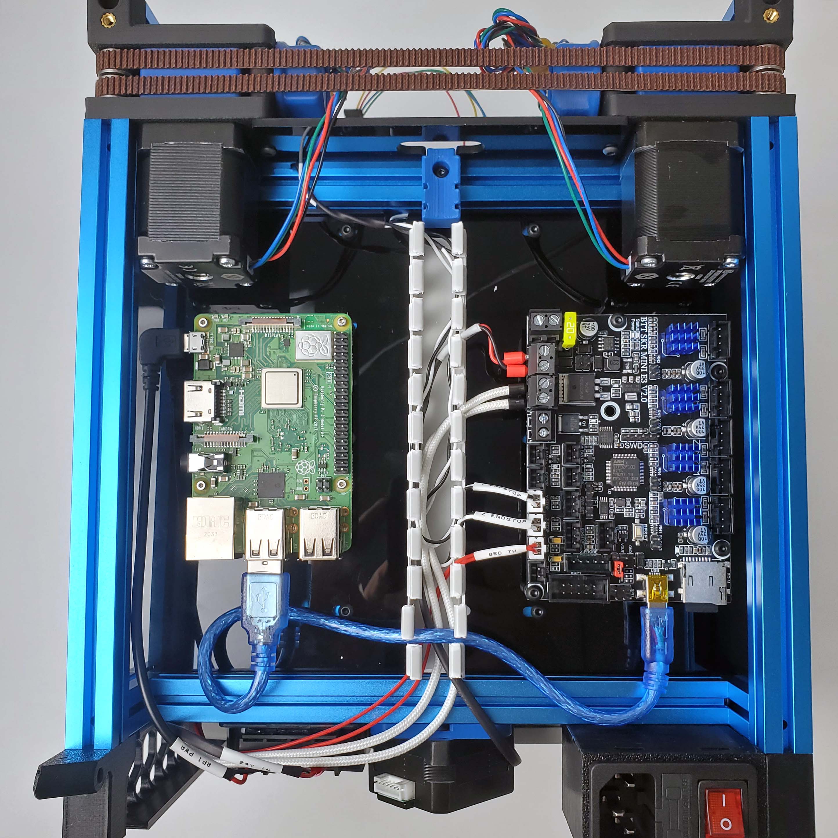
Images/WiringGuide/elec2_complete.jpg
