MotorDynamicsLab/LDOVoron0/Images/WiringGuide/elec3_complete.jpg

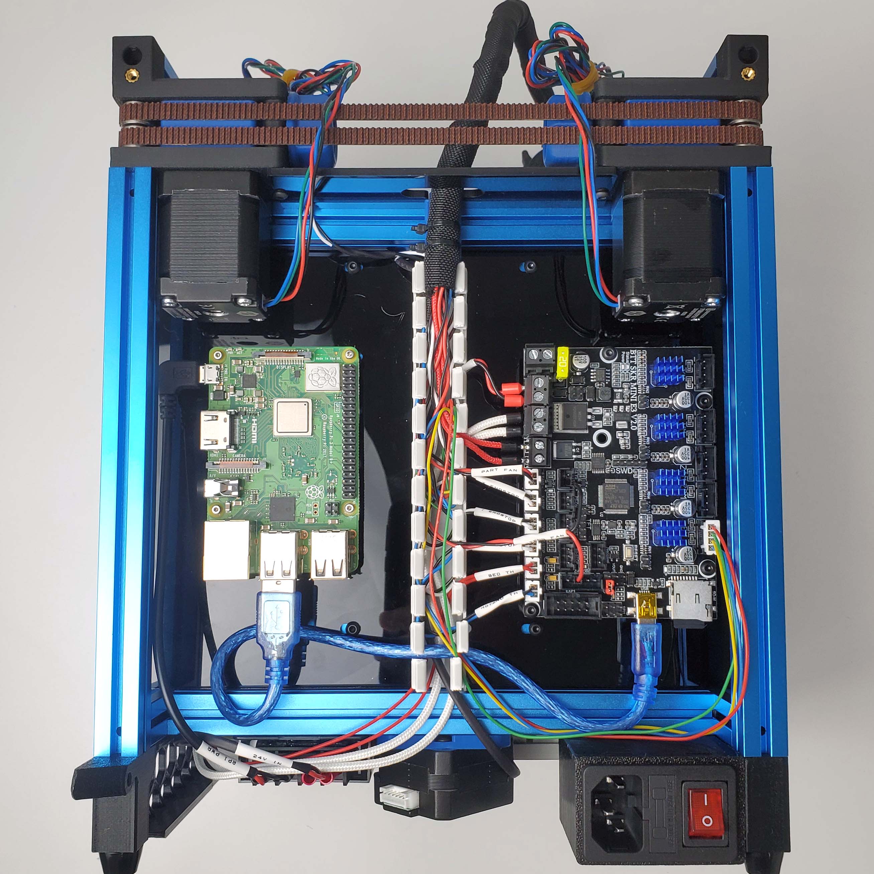
Images/WiringGuide/elec3_complete.jpg
