MotorDynamicsLab/LDOVoron0/Images/WiringGuide/Inlet_Complete.jpg

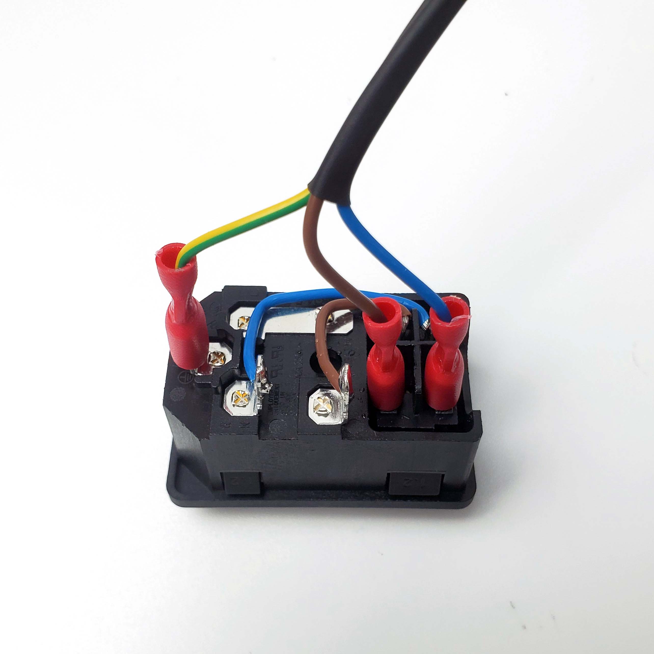
Images/WiringGuide/Inlet_Complete.jpg
