MotorDynamicsLab/LDOVoron0/Images/WiringGuide/Inlet_Layout.png

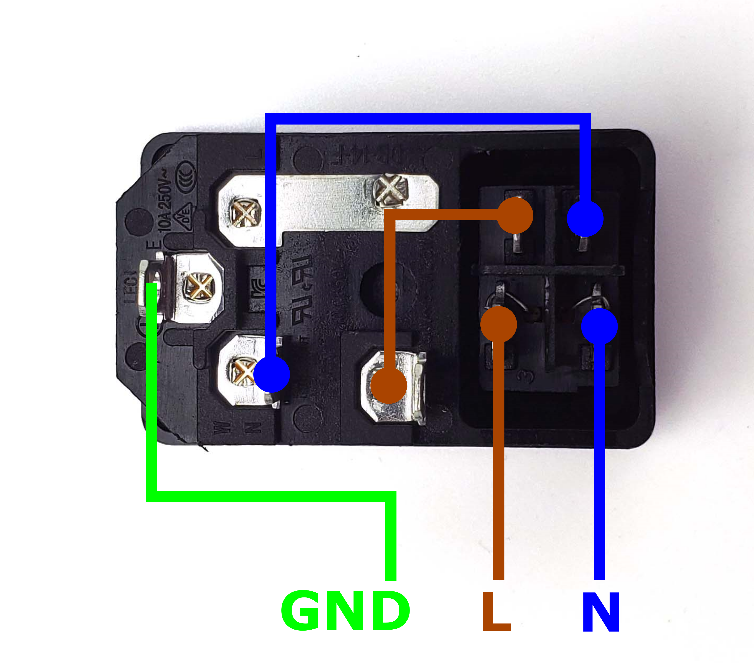
Images/WiringGuide/Inlet_Layout.png
