MotorDynamicsLab/LDOVoron0/Images/WiringGuide/PSU1.jpg

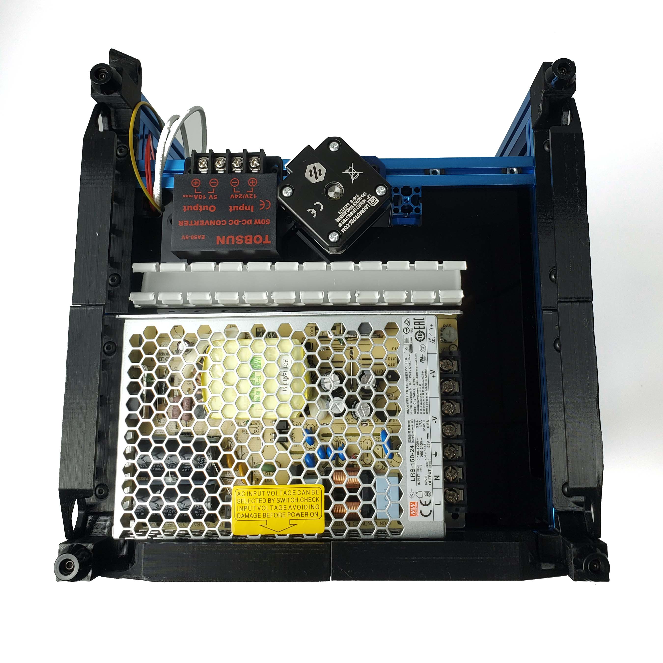
Images/WiringGuide/PSU1.jpg
