MotorDynamicsLab/LDOVoron0/Images/WiringGuide/PSU2.jpg

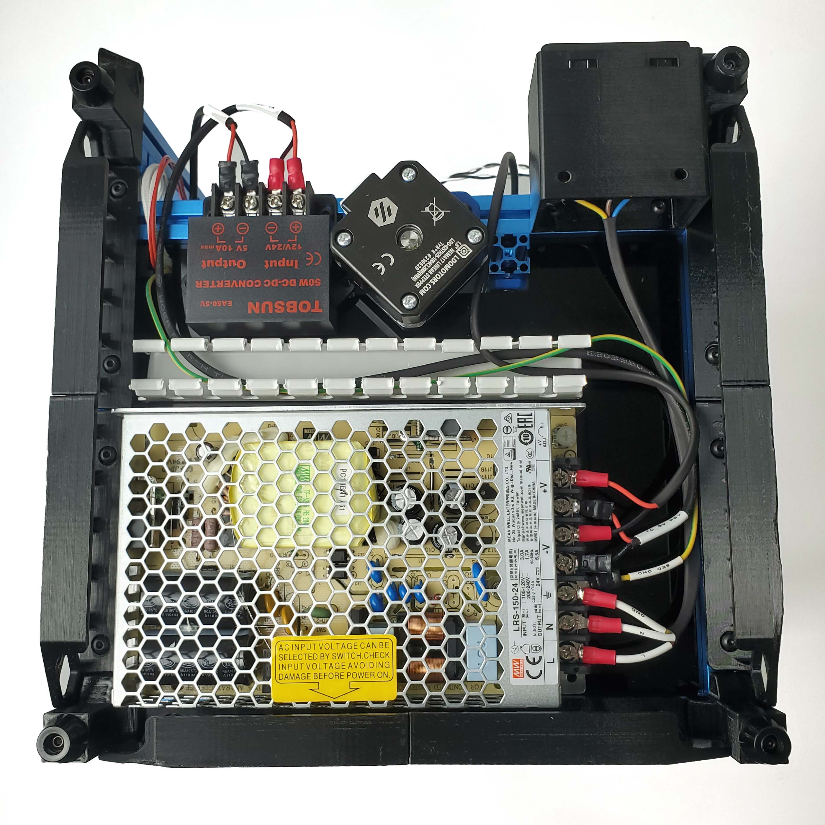
Images/WiringGuide/PSU2.jpg
