MotorDynamicsLab/LDOVoron0/Images/WiringGuide/PSU3.jpg

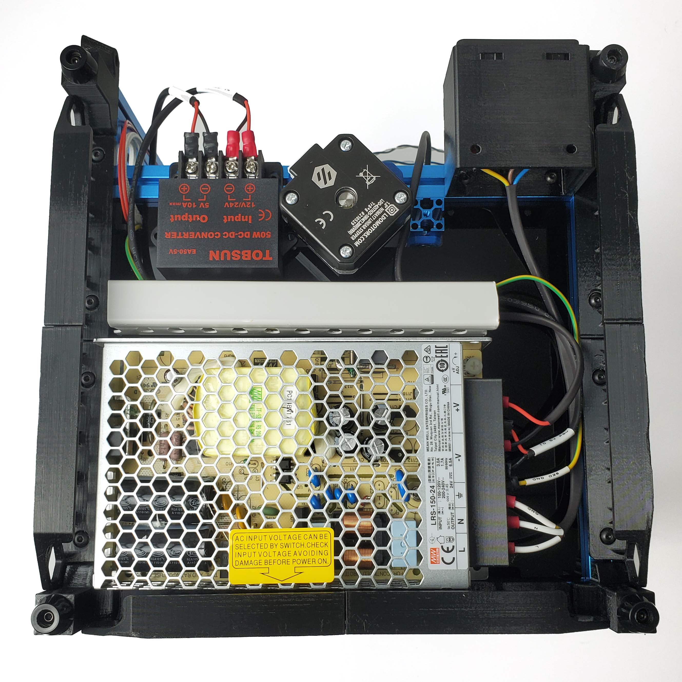
Images/WiringGuide/PSU3.jpg
