MotorDynamicsLab/LDOVoron0/Images/WiringGuide/RawInlet.jpg

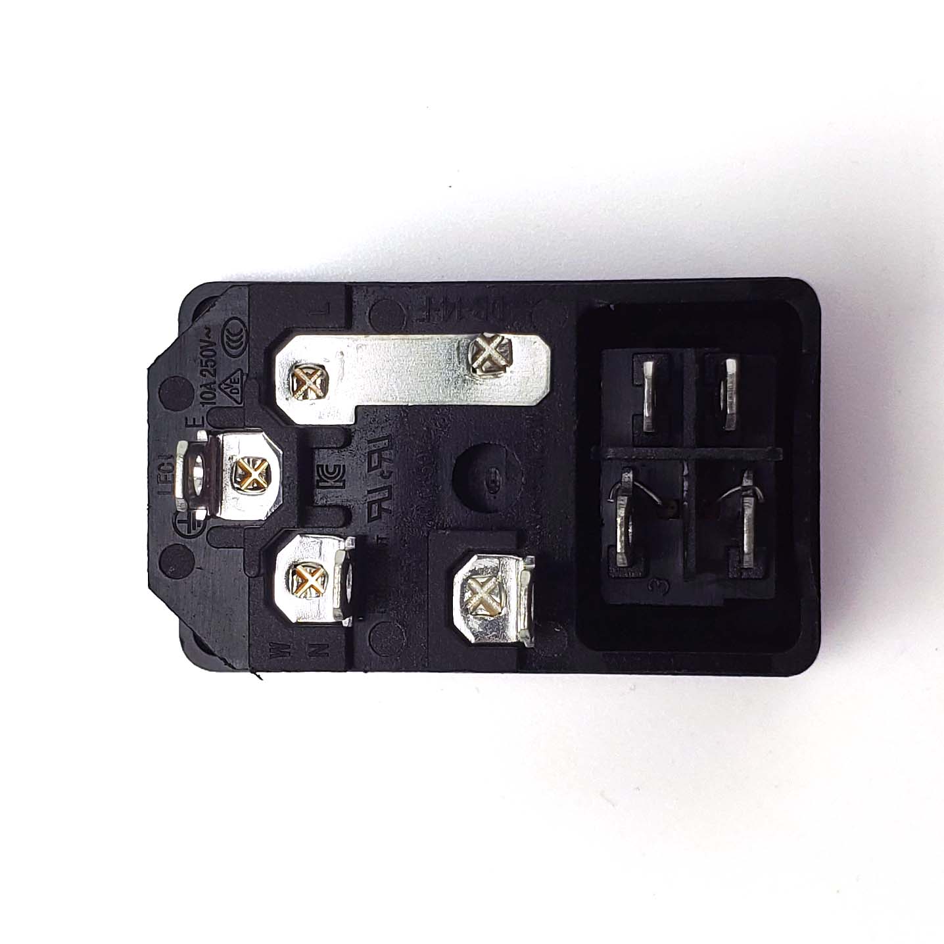
Images/WiringGuide/RawInlet.jpg
