MotorDynamicsLab/LDOVoron0/Images/WiringGuide/S1/s14_fs.jpg

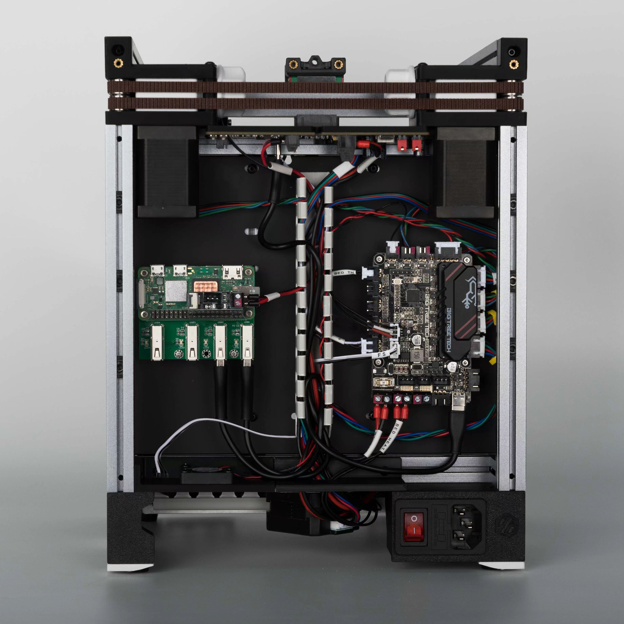
Images/WiringGuide/S1/s14_fs.jpg
