MotorDynamicsLab/LDOVoron0/Images/WiringGuide/S1/s15_toolhead_final.jpg

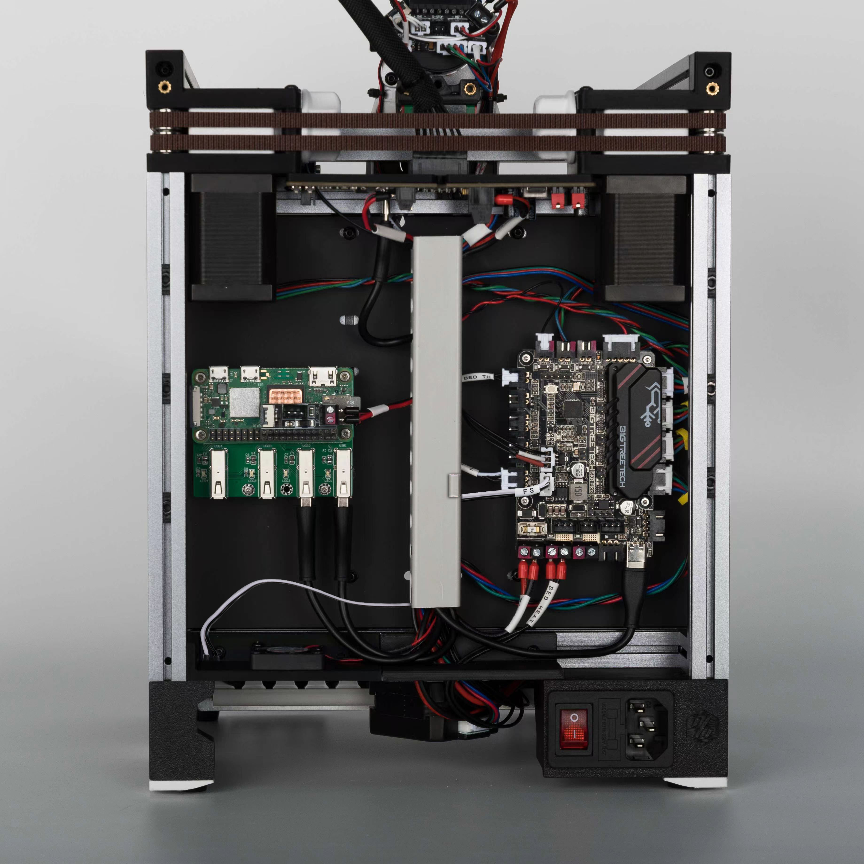
Images/WiringGuide/S1/s15_toolhead_final.jpg
