MotorDynamicsLab/LDOVoron0/Images/WiringGuide/Toolhead1.jpg

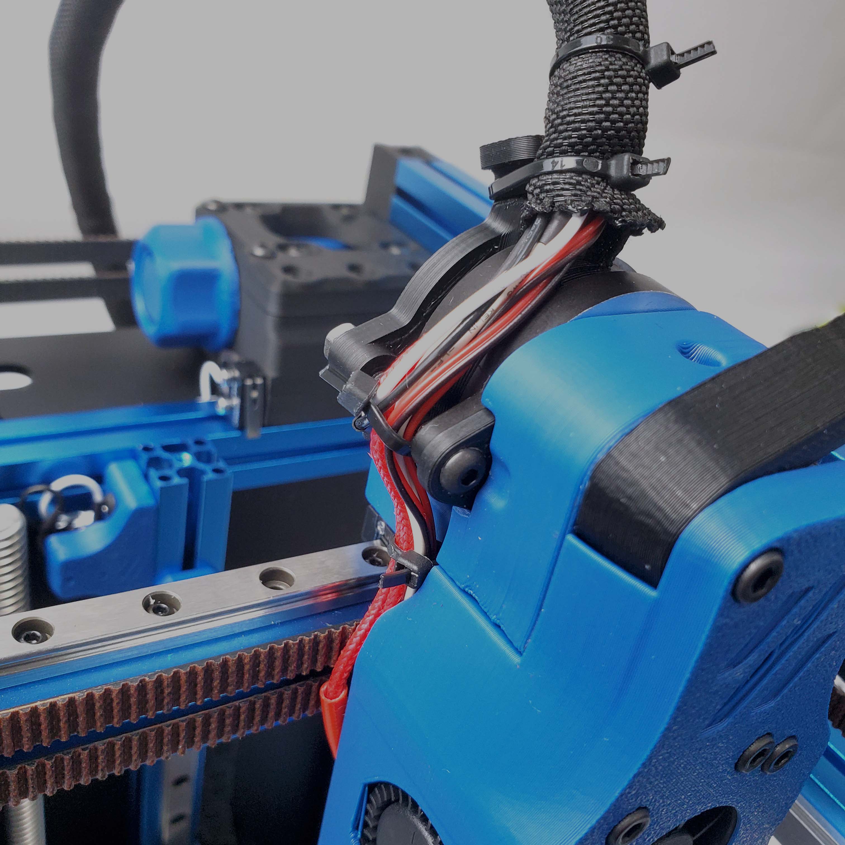
Images/WiringGuide/Toolhead1.jpg
