MotorDynamicsLab/LDOVoron0/Images/WiringGuide/v02/24v_psu_closeup.jpg

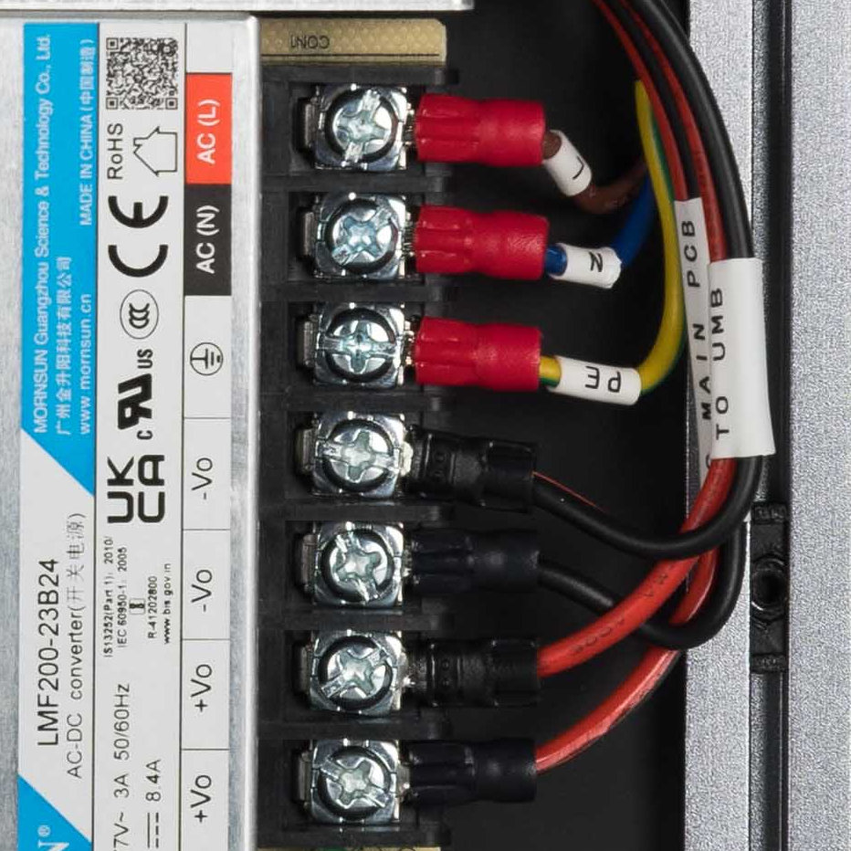
Images/WiringGuide/v02/24v_psu_closeup.jpg
