MotorDynamicsLab/LDOVoron0/Images/WiringGuide/v02/69C2A447.jpeg

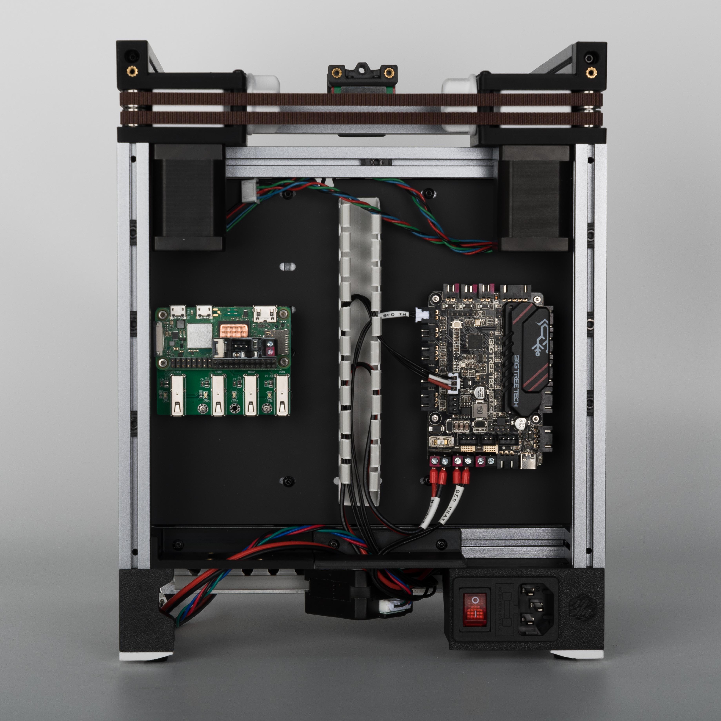
Images/WiringGuide/v02/69C2A447.jpeg
