MotorDynamicsLab/LDOVoron0/Images/WiringGuide/v02/inlet_plugged.JPG

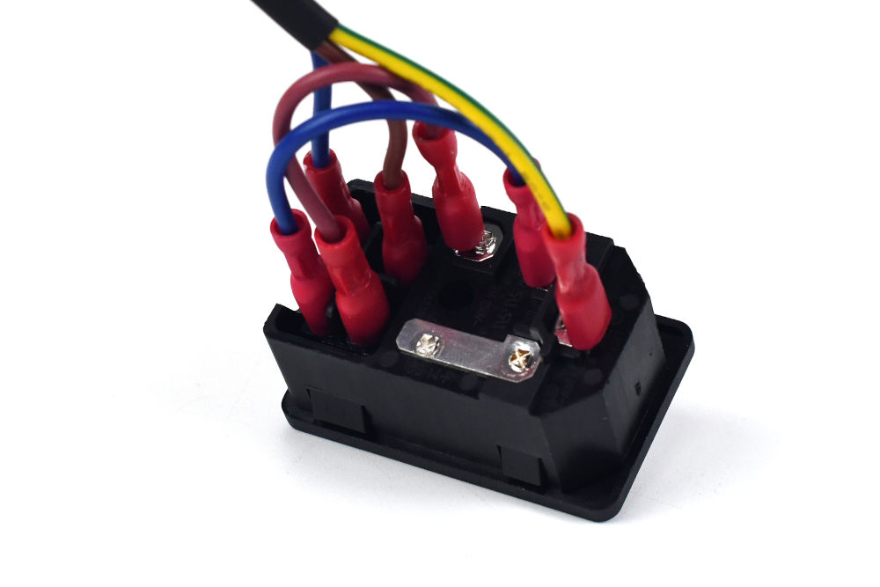
Images/WiringGuide/v02/inlet_plugged.JPG
