MotorDynamicsLab/LDOVoron0/Images/WiringGuide/v02/picobilical_hef_5v_usb_jumper_labelled.jpg

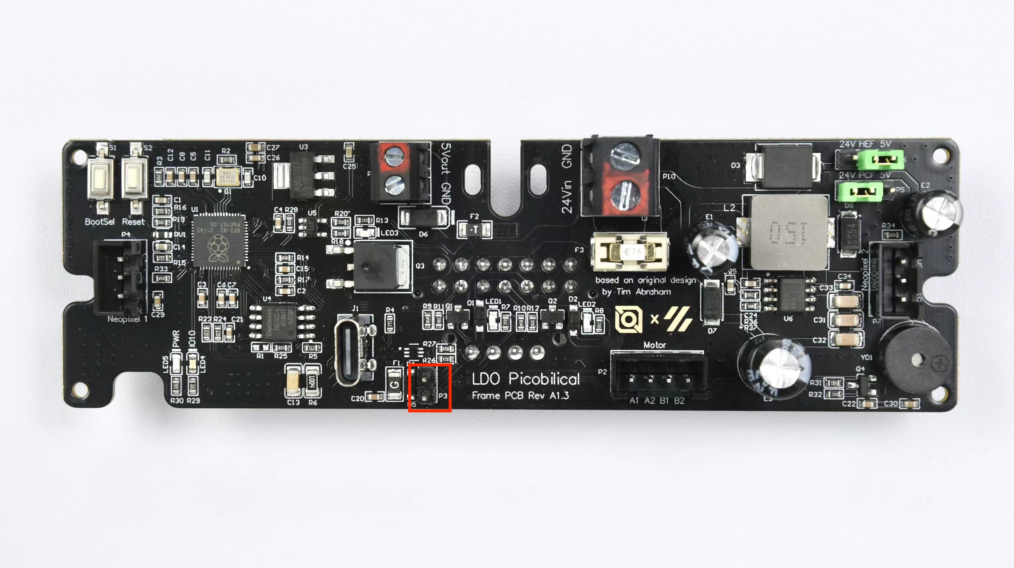
Images/WiringGuide/v02/picobilical_hef_5v_usb_jumper_labelled.jpg
