MotorDynamicsLab/LDOVoron0/Images/WiringGuide/v02/picobilical_prewire.jpg

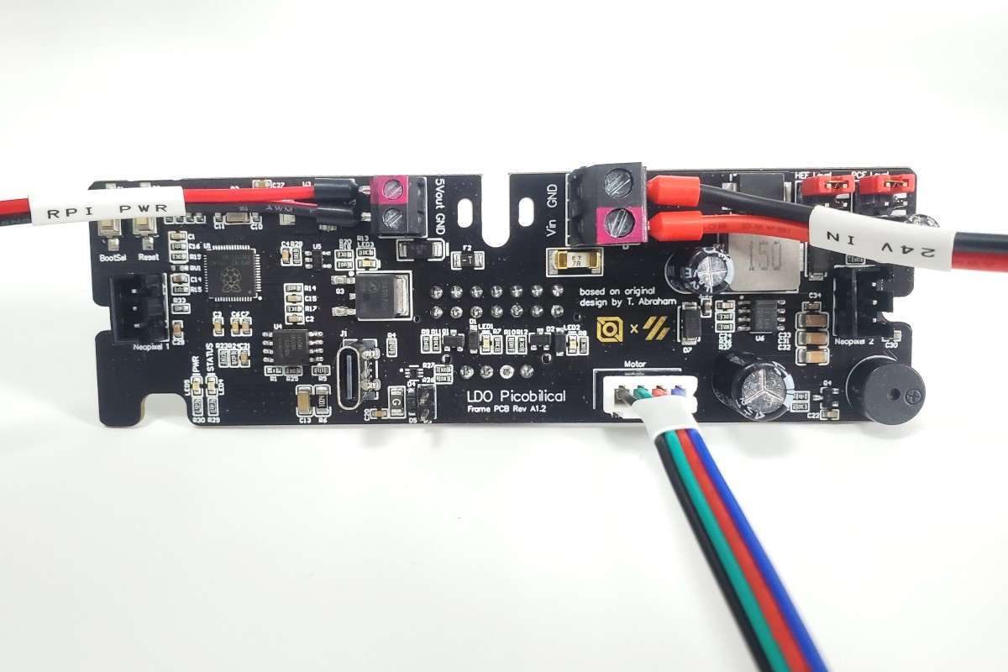
Images/WiringGuide/v02/picobilical_prewire.jpg
