MotorDynamicsLab/LDOVoron0/Images/WiringGuide/v02/picobilical_toolhead.jpg

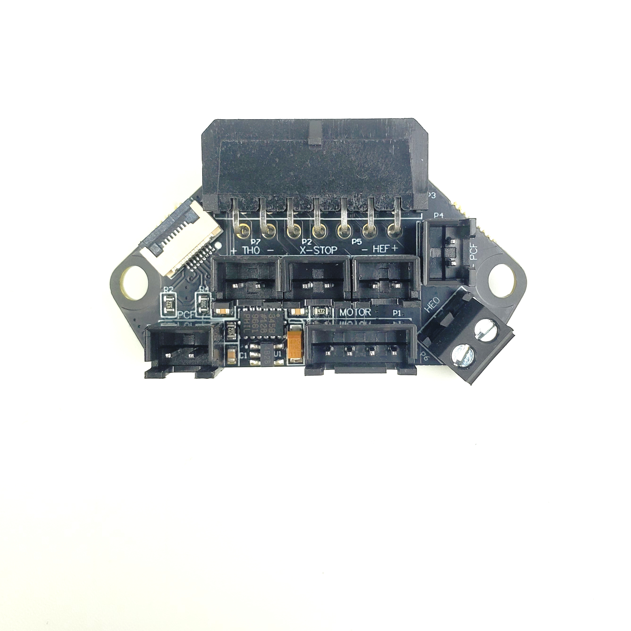
Images/WiringGuide/v02/picobilical_toolhead.jpg
