MotorDynamicsLab/LDOVoron0/Images/WiringGuide/v02/picobilical_toolhead_mapping.png

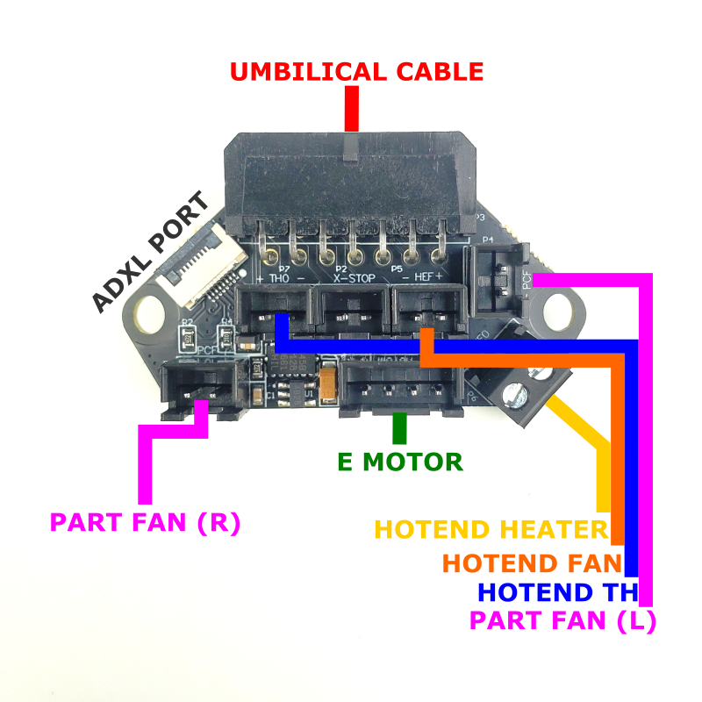
Images/WiringGuide/v02/picobilical_toolhead_mapping.png
