MotorDynamicsLab/LDOVoron0/Images/WiringGuide/v02/psu_switch.jpg

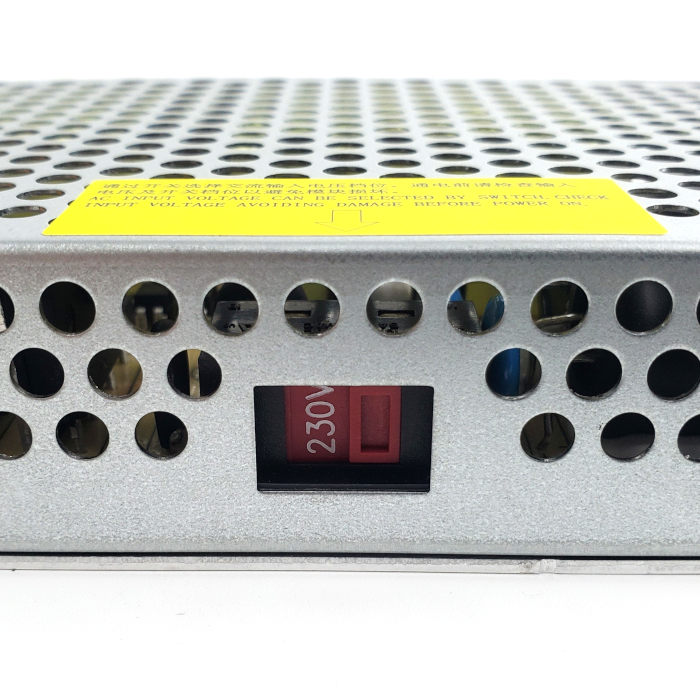
Images/WiringGuide/v02/psu_switch.jpg
