MotorDynamicsLab/LDOVoron0/Images/WiringGuide/v02/rpi_z2w_prep.JPG

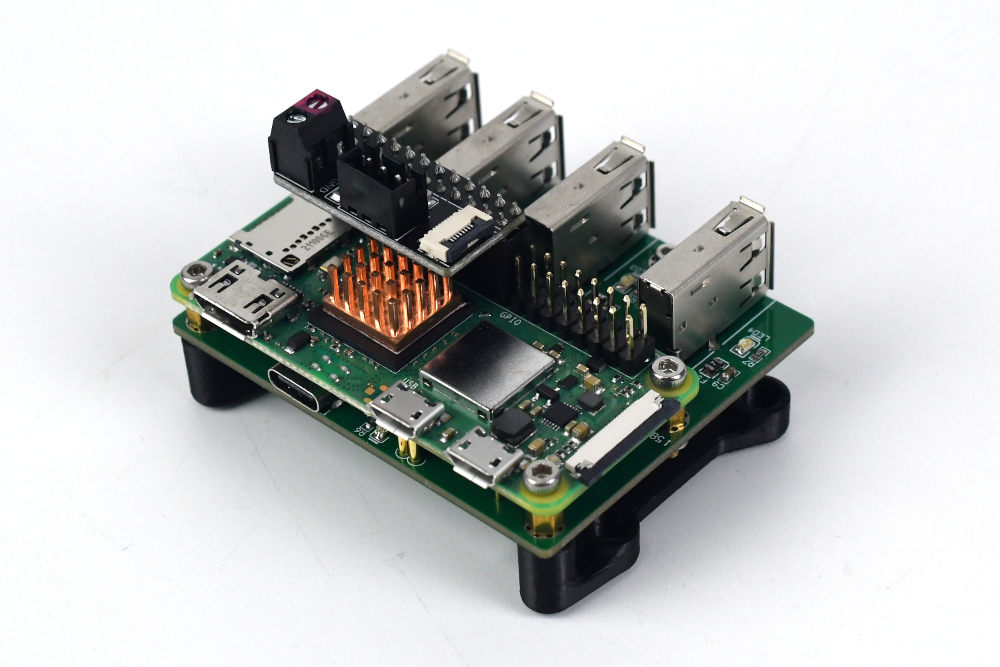
Images/WiringGuide/v02/rpi_z2w_prep.JPG
