MotorDynamicsLab/LDOVoron0/Images/WiringGuide/v02/s01_mapping.png

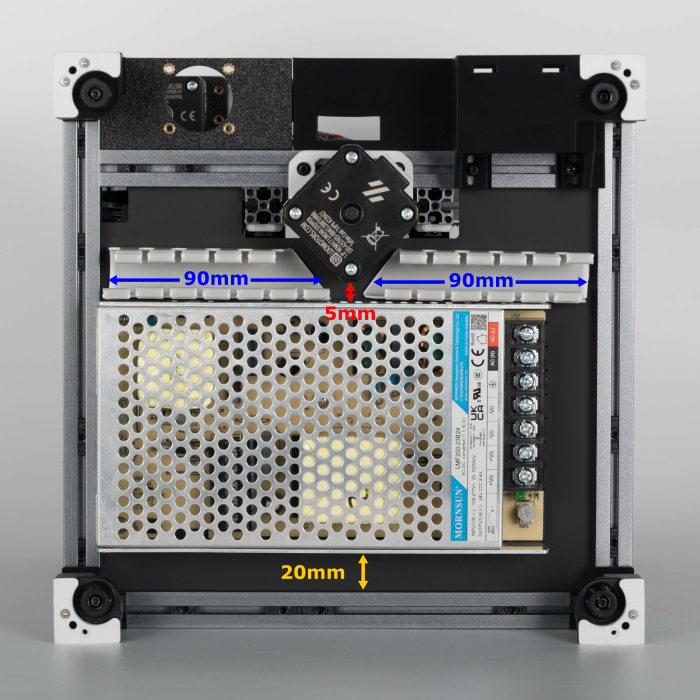
Images/WiringGuide/v02/s01_mapping.png
