MotorDynamicsLab/LDOVoron0/Images/WiringGuide/v02/s02_mapping.png

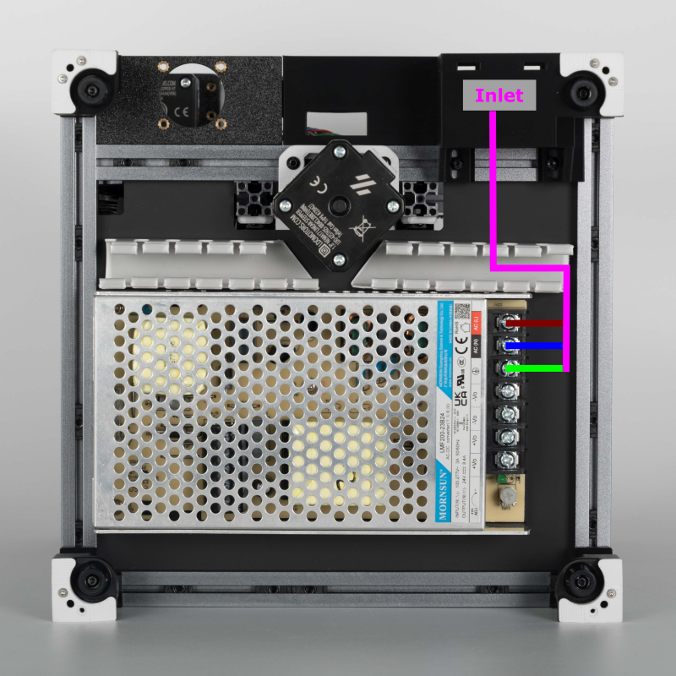
Images/WiringGuide/v02/s02_mapping.png
