MotorDynamicsLab/LDOVoron0/Images/WiringGuide/v02/s03_24v_out.jpg

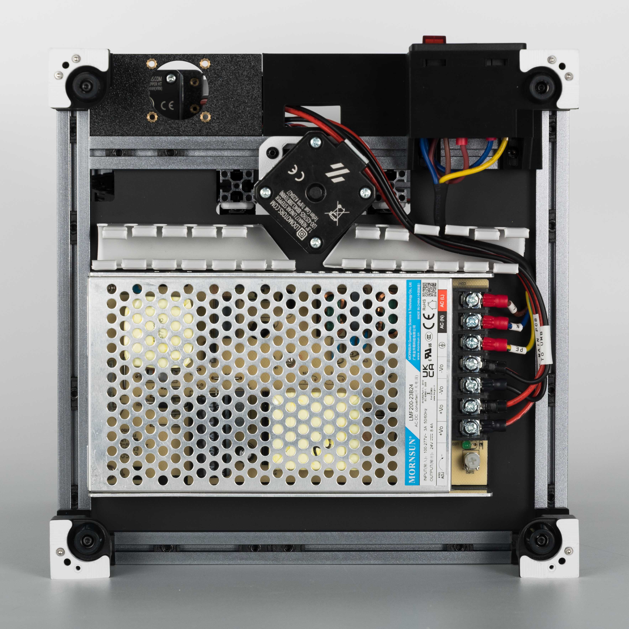
Images/WiringGuide/v02/s03_24v_out.jpg
