MotorDynamicsLab/LDOVoron0/Images/WiringGuide/v02/s07_mapping.png

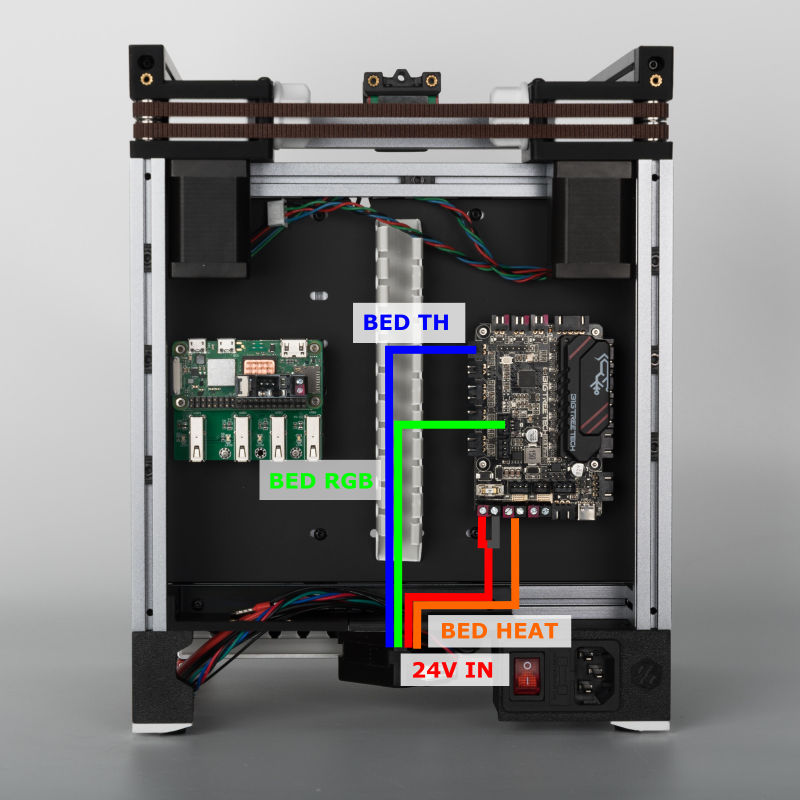
Images/WiringGuide/v02/s07_mapping.png
