MotorDynamicsLab/LDOVoron0/Images/WiringGuide/v02/s09_mapping.png

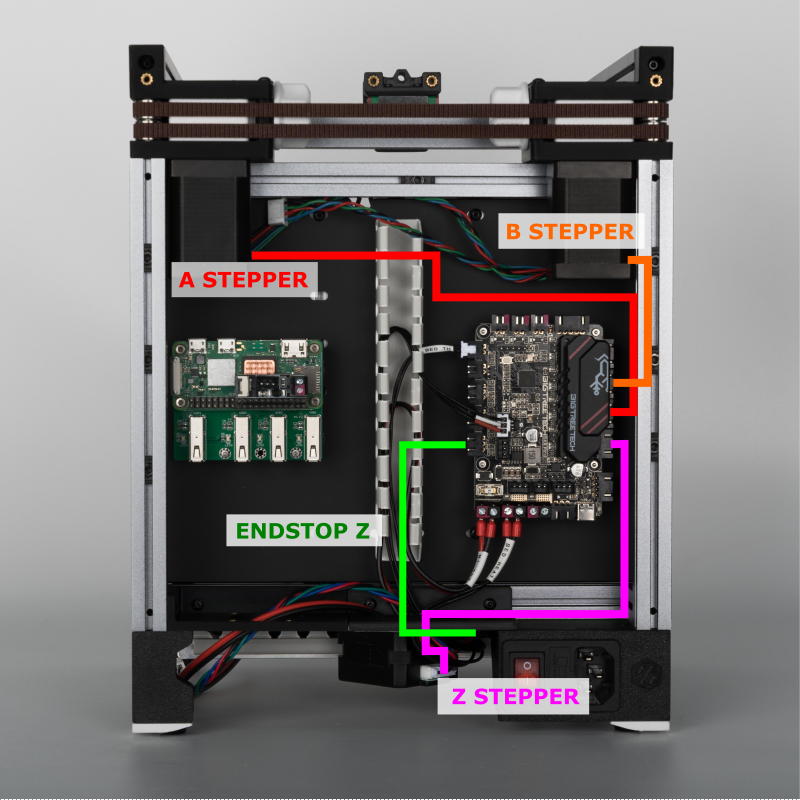
Images/WiringGuide/v02/s09_mapping.png
