MotorDynamicsLab/LDOVoron0/Images/WiringGuide/v02/s10_mapping.png

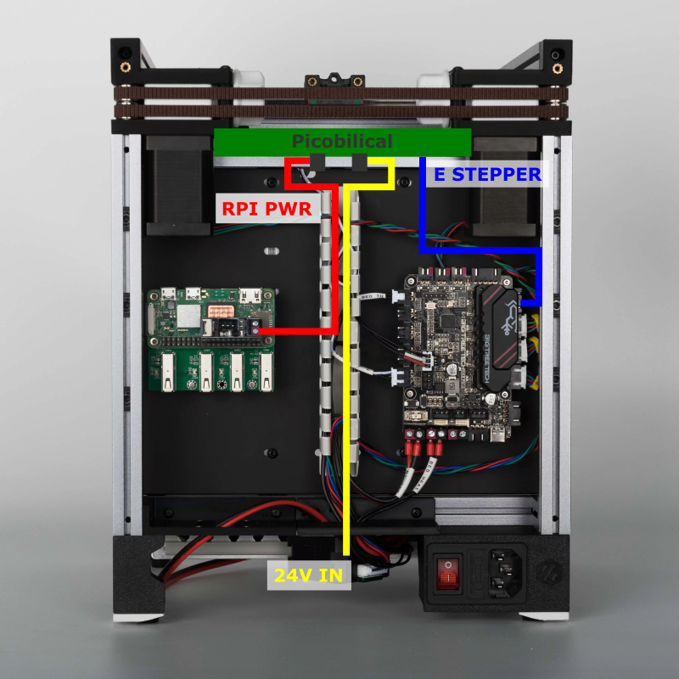
Images/WiringGuide/v02/s10_mapping.png
