MotorDynamicsLab/LDOVoron0/Images/WiringGuide/v02/s12_mapping.png

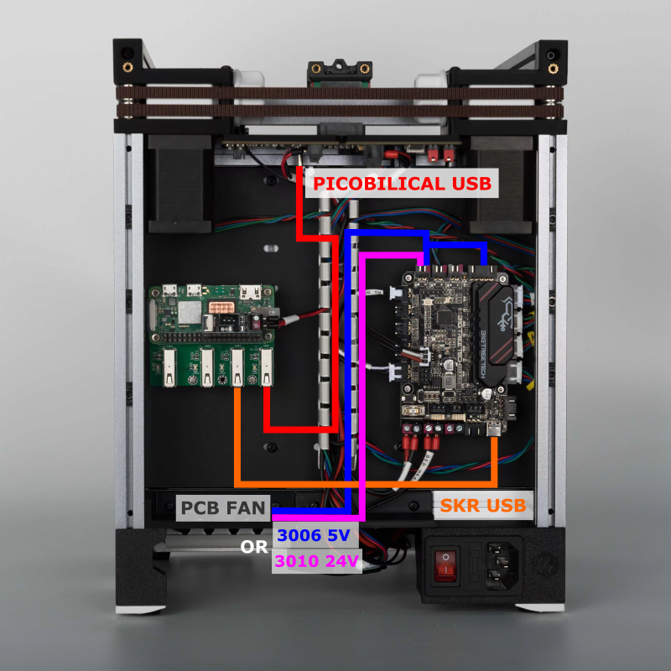
Images/WiringGuide/v02/s12_mapping.png
