MotorDynamicsLab/LDOVoron0/Images/WiringGuide/v02/skr_pico_prep.JPG

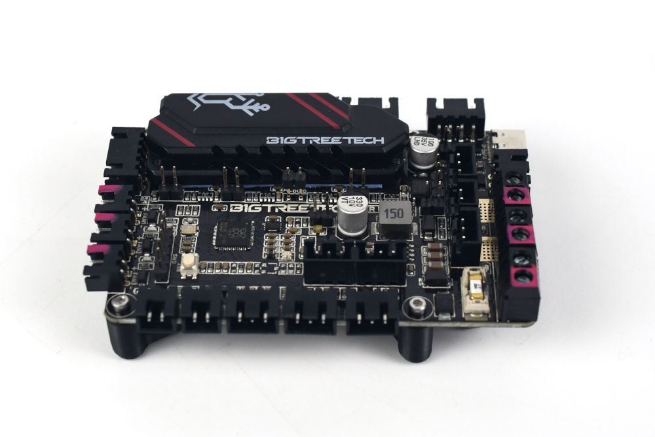
Images/WiringGuide/v02/skr_pico_prep.JPG
