MotorDynamicsLab/LDOVoron0/Images/WiringGuide/v02/skr_pico_prep_usb_jumper_labelled.jpg

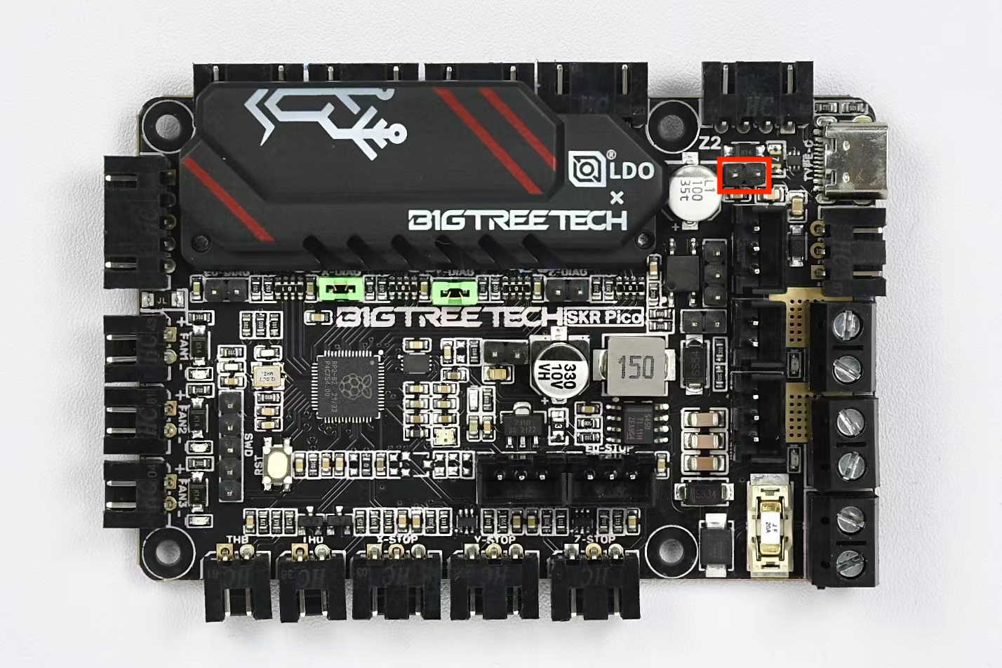
Images/WiringGuide/v02/skr_pico_prep_usb_jumper_labelled.jpg
